VladimirBioACS/VU-meter-IR-control/include/ArduinoJson-v6.19.4.h

// ArduinoJson - https://arduinojson.org
// Copyright © 2014-2022, Benoit BLANCHON
// MIT License

#pragma once

#ifdef __cplusplus

#if __cplusplus >= 201103L
#  define ARDUINOJSON_HAS_LONG_LONG 1
#  define ARDUINOJSON_HAS_RVALUE_REFERENCES 1
#else
#  define ARDUINOJSON_HAS_LONG_LONG 0
#  define ARDUINOJSON_HAS_RVALUE_REFERENCES 0
#endif
#ifndef ARDUINOJSON_HAS_NULLPTR
#  if __cplusplus >= 201103L
#    define ARDUINOJSON_HAS_NULLPTR 1
#  else
#    define ARDUINOJSON_HAS_NULLPTR 0
#  endif
#endif
#if defined(_MSC_VER) && !ARDUINOJSON_HAS_LONG_LONG
#  define ARDUINOJSON_HAS_INT64 1
#else
#  define ARDUINOJSON_HAS_INT64 0
#endif
#ifndef ARDUINOJSON_ENABLE_STD_STREAM
#  ifdef __has_include
#    if __has_include(<istream>) && \
    __has_include(<ostream>) && \
    !defined(min) && \
    !defined(max)
#      define ARDUINOJSON_ENABLE_STD_STREAM 1
#    else
#      define ARDUINOJSON_ENABLE_STD_STREAM 0
#    endif
#  else
#    ifdef ARDUINO
#      define ARDUINOJSON_ENABLE_STD_STREAM 0
#    else
#      define ARDUINOJSON_ENABLE_STD_STREAM 1
#    endif
#  endif
#endif
#ifndef ARDUINOJSON_ENABLE_STD_STRING
#  ifdef __has_include
#    if __has_include(<string>) && !defined(min) && !defined(max)
#      define ARDUINOJSON_ENABLE_STD_STRING 1
#    else
#      define ARDUINOJSON_ENABLE_STD_STRING 0
#    endif
#  else
#    ifdef ARDUINO
#      define ARDUINOJSON_ENABLE_STD_STRING 0
#    else
#      define ARDUINOJSON_ENABLE_STD_STRING 1
#    endif
#  endif
#endif
#ifndef ARDUINOJSON_ENABLE_STRING_VIEW
#  ifdef __has_include
#    if __has_include(<string_view>) && __cplusplus >= 201703L
#      define ARDUINOJSON_ENABLE_STRING_VIEW 1
#    else
#      define ARDUINOJSON_ENABLE_STRING_VIEW 0
#    endif
#  else
#    define ARDUINOJSON_ENABLE_STRING_VIEW 0
#  endif
#endif
#ifndef ARDUINOJSON_USE_DOUBLE
#  define ARDUINOJSON_USE_DOUBLE 1
#endif
#ifndef ARDUINOJSON_USE_LONG_LONG
#  if ARDUINOJSON_HAS_LONG_LONG && defined(__SIZEOF_POINTER__) && \
          __SIZEOF_POINTER__ >= 4 ||                              \
      defined(_MSC_VER)
#    define ARDUINOJSON_USE_LONG_LONG 1
#  endif
#endif
#ifndef ARDUINOJSON_USE_LONG_LONG
#  define ARDUINOJSON_USE_LONG_LONG 0
#endif
#ifndef ARDUINOJSON_DEFAULT_NESTING_LIMIT
#  define ARDUINOJSON_DEFAULT_NESTING_LIMIT 10
#endif
#ifndef ARDUINOJSON_SLOT_OFFSET_SIZE
#  if defined(__SIZEOF_POINTER__) && __SIZEOF_POINTER__ <= 2
#    define ARDUINOJSON_SLOT_OFFSET_SIZE 1
#  elif defined(__SIZEOF_POINTER__) && __SIZEOF_POINTER__ >= 8 || \
      defined(_WIN64) && _WIN64
#    define ARDUINOJSON_SLOT_OFFSET_SIZE 4
#  else
#    define ARDUINOJSON_SLOT_OFFSET_SIZE 2
#  endif
#endif
#ifdef ARDUINO
#  ifndef ARDUINOJSON_ENABLE_ARDUINO_STRING
#    define ARDUINOJSON_ENABLE_ARDUINO_STRING 1
#  endif
#  ifndef ARDUINOJSON_ENABLE_ARDUINO_STREAM
#    define ARDUINOJSON_ENABLE_ARDUINO_STREAM 1
#  endif
#  ifndef ARDUINOJSON_ENABLE_ARDUINO_PRINT
#    define ARDUINOJSON_ENABLE_ARDUINO_PRINT 1
#  endif
#  ifndef ARDUINOJSON_ENABLE_PROGMEM
#    define ARDUINOJSON_ENABLE_PROGMEM 1
#  endif
#else  // ARDUINO
#  ifndef ARDUINOJSON_ENABLE_ARDUINO_STRING
#    define ARDUINOJSON_ENABLE_ARDUINO_STRING 0
#  endif
#  ifndef ARDUINOJSON_ENABLE_ARDUINO_STREAM
#    define ARDUINOJSON_ENABLE_ARDUINO_STREAM 0
#  endif
#  ifndef ARDUINOJSON_ENABLE_ARDUINO_PRINT
#    define ARDUINOJSON_ENABLE_ARDUINO_PRINT 0
#  endif
#  ifndef ARDUINOJSON_ENABLE_PROGMEM
#    define ARDUINOJSON_ENABLE_PROGMEM 0
#  endif
#endif  // ARDUINO
#ifndef ARDUINOJSON_DECODE_UNICODE
#  define ARDUINOJSON_DECODE_UNICODE 1
#endif
#ifndef ARDUINOJSON_ENABLE_COMMENTS
#  define ARDUINOJSON_ENABLE_COMMENTS 0
#endif
#ifndef ARDUINOJSON_ENABLE_NAN
#  define ARDUINOJSON_ENABLE_NAN 0
#endif
#ifndef ARDUINOJSON_ENABLE_INFINITY
#  define ARDUINOJSON_ENABLE_INFINITY 0
#endif
#ifndef ARDUINOJSON_POSITIVE_EXPONENTIATION_THRESHOLD
#  define ARDUINOJSON_POSITIVE_EXPONENTIATION_THRESHOLD 1e7
#endif
#ifndef ARDUINOJSON_NEGATIVE_EXPONENTIATION_THRESHOLD
#  define ARDUINOJSON_NEGATIVE_EXPONENTIATION_THRESHOLD 1e-5
#endif
#ifndef ARDUINOJSON_LITTLE_ENDIAN
#  if defined(_MSC_VER) ||                           \
      (defined(__BYTE_ORDER__) &&                    \
       __BYTE_ORDER__ == __ORDER_LITTLE_ENDIAN__) || \
      defined(__LITTLE_ENDIAN__) || defined(__i386) || defined(__x86_64)
#    define ARDUINOJSON_LITTLE_ENDIAN 1
#  else
#    define ARDUINOJSON_LITTLE_ENDIAN 0
#  endif
#endif
#ifndef ARDUINOJSON_ENABLE_ALIGNMENT
#  if defined(__AVR)
#    define ARDUINOJSON_ENABLE_ALIGNMENT 0
#  else
#    define ARDUINOJSON_ENABLE_ALIGNMENT 1
#  endif
#endif
#ifndef ARDUINOJSON_TAB
#  define ARDUINOJSON_TAB "  "
#endif
#ifndef ARDUINOJSON_ENABLE_STRING_DEDUPLICATION
#  define ARDUINOJSON_ENABLE_STRING_DEDUPLICATION 1
#endif
#ifndef ARDUINOJSON_STRING_BUFFER_SIZE
#  define ARDUINOJSON_STRING_BUFFER_SIZE 32
#endif
#ifndef ARDUINOJSON_DEBUG
#  ifdef __PLATFORMIO_BUILD_DEBUG__
#    define ARDUINOJSON_DEBUG 1
#  else
#    define ARDUINOJSON_DEBUG 0
#  endif
#endif
#if ARDUINOJSON_HAS_NULLPTR && defined(nullptr)
#  error nullptr is defined as a macro. Remove the faulty #define or #undef nullptr
#endif
#if ARDUINOJSON_ENABLE_ARDUINO_STRING || ARDUINOJSON_ENABLE_ARDUINO_STREAM || \
    ARDUINOJSON_ENABLE_ARDUINO_PRINT || ARDUINOJSON_ENABLE_PROGMEM
#include <Arduino.h>
#endif
#if !ARDUINOJSON_DEBUG
#  ifdef __clang__
#    pragma clang system_header
#  elif defined __GNUC__
#    pragma GCC system_header
#  endif
#endif
#define ARDUINOJSON_EXPAND6(a, b, c, d, e, f) a, b, c, d, e, f
#define ARDUINOJSON_EXPAND9(a, b, c, d, e, f, g, h, i) a, b, c, d, e, f, g, h, i
#define ARDUINOJSON_EXPAND18(a, b, c, d, e, f, g, h, i, j, k, l, m, n, o, p, \
                             q, r)                                           \
  a, b, c, d, e, f, g, h, i, j, k, l, m, n, o, p, q, r
#define ARDUINOJSON_CONCAT_(A, B) A##B
#define ARDUINOJSON_CONCAT2(A, B) ARDUINOJSON_CONCAT_(A, B)
#define ARDUINOJSON_CONCAT4(A, B, C, D) \
  ARDUINOJSON_CONCAT2(ARDUINOJSON_CONCAT2(A, B), ARDUINOJSON_CONCAT2(C, D))
#define ARDUINOJSON_HEX_DIGIT_0000() 0
#define ARDUINOJSON_HEX_DIGIT_0001() 1
#define ARDUINOJSON_HEX_DIGIT_0010() 2
#define ARDUINOJSON_HEX_DIGIT_0011() 3
#define ARDUINOJSON_HEX_DIGIT_0100() 4
#define ARDUINOJSON_HEX_DIGIT_0101() 5
#define ARDUINOJSON_HEX_DIGIT_0110() 6
#define ARDUINOJSON_HEX_DIGIT_0111() 7
#define ARDUINOJSON_HEX_DIGIT_1000() 8
#define ARDUINOJSON_HEX_DIGIT_1001() 9
#define ARDUINOJSON_HEX_DIGIT_1010() A
#define ARDUINOJSON_HEX_DIGIT_1011() B
#define ARDUINOJSON_HEX_DIGIT_1100() C
#define ARDUINOJSON_HEX_DIGIT_1101() D
#define ARDUINOJSON_HEX_DIGIT_1110() E
#define ARDUINOJSON_HEX_DIGIT_1111() F
#define ARDUINOJSON_HEX_DIGIT_(A, B, C, D) ARDUINOJSON_HEX_DIGIT_##A##B##C##D()
#define ARDUINOJSON_HEX_DIGIT(A, B, C, D) ARDUINOJSON_HEX_DIGIT_(A, B, C, D)
#define ARDUINOJSON_VERSION "6.19.4"
#define ARDUINOJSON_VERSION_MAJOR 6
#define ARDUINOJSON_VERSION_MINOR 19
#define ARDUINOJSON_VERSION_REVISION 4
#ifndef ARDUINOJSON_NAMESPACE
#  define ARDUINOJSON_NAMESPACE                                               \
    ARDUINOJSON_CONCAT4(                                                      \
        ARDUINOJSON_CONCAT4(ArduinoJson, ARDUINOJSON_VERSION_MAJOR,           \
                            ARDUINOJSON_VERSION_MINOR,                        \
                            ARDUINOJSON_VERSION_REVISION),                    \
        _,                                                                    \
        ARDUINOJSON_HEX_DIGIT(                                                \
            ARDUINOJSON_ENABLE_PROGMEM, ARDUINOJSON_USE_LONG_LONG,            \
            ARDUINOJSON_USE_DOUBLE, ARDUINOJSON_ENABLE_STRING_DEDUPLICATION), \
        ARDUINOJSON_HEX_DIGIT(                                                \
            ARDUINOJSON_ENABLE_NAN, ARDUINOJSON_ENABLE_INFINITY,              \
            ARDUINOJSON_ENABLE_COMMENTS, ARDUINOJSON_DECODE_UNICODE))
#endif
#if ARDUINOJSON_DEBUG
#include <assert.h>
#  define ARDUINOJSON_ASSERT(X) assert(X)
#else
#  define ARDUINOJSON_ASSERT(X) ((void)0)
#endif
#include <stddef.h>
namespace ARDUINOJSON_NAMESPACE {
class MemoryPool;
class VariantData;
class VariantSlot;
class CollectionData {
  VariantSlot *_head;
  VariantSlot *_tail;
 public:
  VariantData *addElement(MemoryPool *pool);
  VariantData *getElement(size_t index) const;
  VariantData *getOrAddElement(size_t index, MemoryPool *pool);
  void removeElement(size_t index);
  bool equalsArray(const CollectionData &other) const;
  template <typename TAdaptedString, typename TStoragePolicy>
  VariantData *addMember(TAdaptedString key, MemoryPool *pool, TStoragePolicy);
  template <typename TAdaptedString>
  VariantData *getMember(TAdaptedString key) const;
  template <typename TAdaptedString, typename TStoragePolicy>
  VariantData *getOrAddMember(TAdaptedString key, MemoryPool *pool,
                              TStoragePolicy);
  template <typename TAdaptedString>
  void removeMember(TAdaptedString key) {
    removeSlot(getSlot(key));
  }
  template <typename TAdaptedString>
  bool containsKey(const TAdaptedString &key) const;
  bool equalsObject(const CollectionData &other) const;
  void clear();
  size_t memoryUsage() const;
  size_t nesting() const;
  size_t size() const;
  VariantSlot *addSlot(MemoryPool *);
  void removeSlot(VariantSlot *slot);
  bool copyFrom(const CollectionData &src, MemoryPool *pool);
  VariantSlot *head() const {
    return _head;
  }
  void movePointers(ptrdiff_t stringDistance, ptrdiff_t variantDistance);
 private:
  VariantSlot *getSlot(size_t index) const;
  template <typename TAdaptedString>
  VariantSlot *getSlot(TAdaptedString key) const;
  VariantSlot *getPreviousSlot(VariantSlot *) const;
};
inline VariantData *arrayAdd(CollectionData *arr, MemoryPool *pool) {
  return arr ? arr->addElement(pool) : 0;
}
template <typename TVisitor>
inline typename TVisitor::result_type arrayAccept(const CollectionData *arr,
                                                  TVisitor &visitor) {
  if (arr)
    return visitor.visitArray(*arr);
  else
    return visitor.visitNull();
}
inline bool arrayEquals(const CollectionData *lhs, const CollectionData *rhs) {
  if (lhs == rhs)
    return true;
  if (!lhs || !rhs)
    return false;
  return lhs->equalsArray(*rhs);
}
#if ARDUINOJSON_ENABLE_ALIGNMENT
inline bool isAligned(size_t value) {
  const size_t mask = sizeof(void *) - 1;
  size_t addr = value;
  return (addr & mask) == 0;
}
inline size_t addPadding(size_t bytes) {
  const size_t mask = sizeof(void *) - 1;
  return (bytes + mask) & ~mask;
}
template <size_t bytes>
struct AddPadding {
  static const size_t mask = sizeof(void *) - 1;
  static const size_t value = (bytes + mask) & ~mask;
};
#else
inline bool isAligned(size_t) {
  return true;
}
inline size_t addPadding(size_t bytes) {
  return bytes;
}
template <size_t bytes>
struct AddPadding {
  static const size_t value = bytes;
};
#endif
template <typename T>
inline bool isAligned(T *ptr) {
  return isAligned(reinterpret_cast<size_t>(ptr));
}
template <typename T>
inline T *addPadding(T *p) {
  size_t address = addPadding(reinterpret_cast<size_t>(p));
  return reinterpret_cast<T *>(address);
}
template <size_t X, size_t Y, bool MaxIsX = (X > Y)>
struct Max {};
template <size_t X, size_t Y>
struct Max<X, Y, true> {
  static const size_t value = X;
};
template <size_t X, size_t Y>
struct Max<X, Y, false> {
  static const size_t value = Y;
};
template <bool Condition, class TrueType, class FalseType>
struct conditional {
  typedef TrueType type;
};
template <class TrueType, class FalseType>
struct conditional<false, TrueType, FalseType> {
  typedef FalseType type;
};
template <bool Condition, typename T = void>
struct enable_if {};
template <typename T>
struct enable_if<true, T> {
  typedef T type;
};
template <typename T, T v>
struct integral_constant {
  static const T value = v;
};
typedef integral_constant<bool, true> true_type;
typedef integral_constant<bool, false> false_type;
template <typename T>
struct is_array : false_type {};
template <typename T>
struct is_array<T[]> : true_type {};
template <typename T, size_t N>
struct is_array<T[N]> : true_type {};
template <typename TBase, typename TDerived>
class is_base_of {
 protected:  // <- to avoid GCC's "all member functions in class are private"
  typedef char Yes[1];
  typedef char No[2];
  static Yes &probe(const TBase *);
  static No &probe(...);
 public:
  static const bool value =
      sizeof(probe(reinterpret_cast<TDerived *>(0))) == sizeof(Yes);
};
template <typename T>
T declval();
template <typename T>
struct is_class {
 protected:  // <- to avoid GCC's "all member functions in class are private"
  typedef char Yes[1];
  typedef char No[2];
  template <typename U>
  static Yes &probe(void (U::*)(void));
  template <typename>
  static No &probe(...);
 public:
  static const bool value = sizeof(probe<T>(0)) == sizeof(Yes);
};
template <typename T>
struct is_const : false_type {};
template <typename T>
struct is_const<const T> : true_type {};
}  // namespace ARDUINOJSON_NAMESPACE
#ifdef _MSC_VER
#  pragma warning(push)
#  pragma warning(disable : 4244)
#endif
#ifdef __ICCARM__
#pragma diag_suppress=Pa093
#endif
namespace ARDUINOJSON_NAMESPACE {
template <typename From, typename To>
struct is_convertible {
 protected:  // <- to avoid GCC's "all member functions in class are private"
  typedef char Yes[1];
  typedef char No[2];
  static Yes &probe(To);
  static No &probe(...);
 public:
  static const bool value = sizeof(probe(declval<From>())) == sizeof(Yes);
};
}  // namespace ARDUINOJSON_NAMESPACE
#ifdef _MSC_VER
#  pragma warning(pop)
#endif
#ifdef __ICCARM__
#pragma diag_default=Pa093
#endif
namespace ARDUINOJSON_NAMESPACE {
template <typename T, typename U>
struct is_same : false_type {};
template <typename T>
struct is_same<T, T> : true_type {};
template <typename T>
struct remove_cv {
  typedef T type;
};
template <typename T>
struct remove_cv<const T> {
  typedef T type;
};
template <typename T>
struct remove_cv<volatile T> {
  typedef T type;
};
template <typename T>
struct remove_cv<const volatile T> {
  typedef T type;
};
template <class T>
struct is_floating_point
    : integral_constant<
          bool,  //
          is_same<float, typename remove_cv<T>::type>::value ||
              is_same<double, typename remove_cv<T>::type>::value> {};
template <typename T>
struct is_integral : integral_constant<bool,
    is_same<typename remove_cv<T>::type, signed char>::value ||
    is_same<typename remove_cv<T>::type, unsigned char>::value ||
    is_same<typename remove_cv<T>::type, signed short>::value ||
    is_same<typename remove_cv<T>::type, unsigned short>::value ||
    is_same<typename remove_cv<T>::type, signed int>::value ||
    is_same<typename remove_cv<T>::type, unsigned int>::value ||
    is_same<typename remove_cv<T>::type, signed long>::value ||
    is_same<typename remove_cv<T>::type, unsigned long>::value ||
#if ARDUINOJSON_HAS_LONG_LONG
    is_same<typename remove_cv<T>::type, signed long long>::value ||
    is_same<typename remove_cv<T>::type, unsigned long long>::value ||
#endif
#if ARDUINOJSON_HAS_INT64
    is_same<typename remove_cv<T>::type, signed __int64>::value ||
    is_same<typename remove_cv<T>::type, unsigned __int64>::value ||
#endif
    is_same<typename remove_cv<T>::type, char>::value ||
    is_same<typename remove_cv<T>::type, bool>::value> {};
template <typename T>
struct is_enum {
  static const bool value = is_convertible<T, int>::value &&
                            !is_class<T>::value && !is_integral<T>::value &&
                            !is_floating_point<T>::value;
};
template <typename T>
struct is_pointer : false_type {};
template <typename T>
struct is_pointer<T*> : true_type {};
template <typename T>
struct is_signed : integral_constant<bool, 
    is_same<typename remove_cv<T>::type, char>::value ||
    is_same<typename remove_cv<T>::type, signed char>::value ||
    is_same<typename remove_cv<T>::type, signed short>::value ||
    is_same<typename remove_cv<T>::type, signed int>::value ||
    is_same<typename remove_cv<T>::type, signed long>::value ||
#if ARDUINOJSON_HAS_LONG_LONG
    is_same<typename remove_cv<T>::type, signed long long>::value ||
#endif
#if ARDUINOJSON_HAS_INT64
    is_same<typename remove_cv<T>::type, signed __int64>::value ||
#endif
    is_same<typename remove_cv<T>::type, float>::value ||
    is_same<typename remove_cv<T>::type, double>::value> {};
template <typename T>
struct is_unsigned : integral_constant<bool,
    is_same<typename remove_cv<T>::type, unsigned char>::value ||
    is_same<typename remove_cv<T>::type, unsigned short>::value ||
    is_same<typename remove_cv<T>::type, unsigned int>::value ||
    is_same<typename remove_cv<T>::type, unsigned long>::value ||
#if ARDUINOJSON_HAS_INT64
    is_same<typename remove_cv<T>::type, unsigned __int64>::value ||
#endif
#if ARDUINOJSON_HAS_LONG_LONG
    is_same<typename remove_cv<T>::type, unsigned long long>::value ||
#endif
    is_same<typename remove_cv<T>::type, bool>::value> {};
template <typename T>
struct type_identity {
  typedef T type;
};
template <typename T>
struct make_unsigned;
template <>
struct make_unsigned<char> : type_identity<unsigned char> {};
template <>
struct make_unsigned<signed char> : type_identity<unsigned char> {};
template <>
struct make_unsigned<unsigned char> : type_identity<unsigned char> {};
template <>
struct make_unsigned<signed short> : type_identity<unsigned short> {};
template <>
struct make_unsigned<unsigned short> : type_identity<unsigned short> {};
template <>
struct make_unsigned<signed int> : type_identity<unsigned int> {};
template <>
struct make_unsigned<unsigned int> : type_identity<unsigned int> {};
template <>
struct make_unsigned<signed long> : type_identity<unsigned long> {};
template <>
struct make_unsigned<unsigned long> : type_identity<unsigned long> {};
#if ARDUINOJSON_HAS_LONG_LONG
template <>
struct make_unsigned<signed long long> : type_identity<unsigned long long> {};
template <>
struct make_unsigned<unsigned long long> : type_identity<unsigned long long> {};
#endif
#if ARDUINOJSON_HAS_INT64
template <>
struct make_unsigned<signed __int64> : type_identity<unsigned __int64> {};
template <>
struct make_unsigned<unsigned __int64> : type_identity<unsigned __int64> {};
#endif
template <class = void>
struct make_void {
  typedef void type;
};
template <typename T>
struct remove_const {
  typedef T type;
};
template <typename T>
struct remove_const<const T> {
  typedef T type;
};
template <typename T>
struct remove_reference {
  typedef T type;
};
template <typename T>
struct remove_reference<T&> {
  typedef T type;
};
}  // namespace ARDUINOJSON_NAMESPACE
#include <string.h>
namespace ARDUINOJSON_NAMESPACE {
template <typename T, typename Enable = void>
struct IsString : false_type {};
template <typename TChar>
struct IsString<const TChar*> : IsString<TChar*> {};
class ZeroTerminatedRamString {
 public:
  static const size_t typeSortKey = 3;
  ZeroTerminatedRamString(const char* str) : _str(str) {}
  bool isNull() const {
    return !_str;
  }
  size_t size() const {
    return _str ? ::strlen(_str) : 0;
  }
  char operator[](size_t i) const {
    ARDUINOJSON_ASSERT(_str != 0);
    ARDUINOJSON_ASSERT(i <= size());
    return _str[i];
  }
  const char* data() const {
    return _str;
  }
  friend int stringCompare(ZeroTerminatedRamString a,
                           ZeroTerminatedRamString b) {
    ARDUINOJSON_ASSERT(!a.isNull());
    ARDUINOJSON_ASSERT(!b.isNull());
    return ::strcmp(a._str, b._str);
  }
  friend bool stringEquals(ZeroTerminatedRamString a,
                           ZeroTerminatedRamString b) {
    return stringCompare(a, b) == 0;
  }
 protected:
  const char* _str;
};
template <>
struct IsString<char*> : true_type {};
inline ZeroTerminatedRamString adaptString(const char* s) {
  return ZeroTerminatedRamString(s);
}
template <>
struct IsString<unsigned char*> : true_type {};
inline ZeroTerminatedRamString adaptString(const unsigned char* s) {
  return adaptString(reinterpret_cast<const char*>(s));
}
template <>
struct IsString<signed char*> : true_type {};
inline ZeroTerminatedRamString adaptString(const signed char* s) {
  return adaptString(reinterpret_cast<const char*>(s));
}
class SizedRamString {
 public:
  static const size_t typeSortKey = 2;
  SizedRamString(const char* str, size_t sz) : _str(str), _size(sz) {}
  bool isNull() const {
    return !_str;
  }
  size_t size() const {
    return _size;
  }
  char operator[](size_t i) const {
    ARDUINOJSON_ASSERT(_str != 0);
    ARDUINOJSON_ASSERT(i <= size());
    return _str[i];
  }
  const char* data() const {
    return _str;
  }
 protected:
  const char* _str;
  size_t _size;
};
inline SizedRamString adaptString(const char* s, size_t n) {
  return SizedRamString(s, n);
}
template <size_t N>
struct IsString<char[N]> : true_type {};
template <size_t N>
struct IsString<const char[N]> : true_type {};
template <size_t N>
inline SizedRamString adaptString(char s[N]) {
  return SizedRamString(s, strlen(s));
}
template <typename T>
class SafeBoolIdom {
 protected:
  typedef void (T::*bool_type)() const;
  void safeBoolHelper() const {}
  static bool_type safe_true() {
    return &SafeBoolIdom::safeBoolHelper;
  }
  static bool_type safe_false() {
    return 0;
  }
};
}  // namespace ARDUINOJSON_NAMESPACE
#if ARDUINOJSON_ENABLE_STD_STREAM
#include <ostream>
#endif
namespace ARDUINOJSON_NAMESPACE {
class String : public SafeBoolIdom<String> {
 public:
  enum Ownership { Copied, Linked };
  String() : _data(0), _size(0), _ownership(Linked) {}
  String(const char* data, Ownership ownership = Linked)
      : _data(data), _size(data ? ::strlen(data) : 0), _ownership(ownership) {}
  String(const char* data, size_t sz, Ownership ownership = Linked)
      : _data(data), _size(sz), _ownership(ownership) {}
  const char* c_str() const {
    return _data;
  }
  bool isNull() const {
    return !_data;
  }
  bool isLinked() const {
    return _ownership == Linked;
  }
  size_t size() const {
    return _size;
  }
  operator bool_type() const {
    return _data ? safe_true() : safe_false();
  }
  friend bool operator==(String lhs, String rhs) {
    if (lhs._size != rhs._size)
      return false;
    if (lhs._data == rhs._data)
      return true;
    if (!lhs._data)
      return false;
    if (!rhs._data)
      return false;
    return memcmp(lhs._data, rhs._data, lhs._size) == 0;
  }
  friend bool operator!=(String lhs, String rhs) {
    return !(lhs == rhs);
  }
#if ARDUINOJSON_ENABLE_STD_STREAM
  friend std::ostream& operator<<(std::ostream& lhs, const String& rhs) {
    lhs.write(rhs.c_str(), static_cast<std::streamsize>(rhs.size()));
    return lhs;
  }
#endif
 private:
  const char* _data;
  size_t _size;
  Ownership _ownership;
};
inline SizedRamString adaptString(const String& s) {
  return SizedRamString(s.c_str(), s.size());
}
template <>
struct IsString<String> : true_type {};
}  // namespace ARDUINOJSON_NAMESPACE
#if ARDUINOJSON_ENABLE_STD_STRING
#include <string>
namespace ARDUINOJSON_NAMESPACE {
template <typename TCharTraits, typename TAllocator>
inline SizedRamString adaptString(
    const std::basic_string<char, TCharTraits, TAllocator>& s) {
  return SizedRamString(s.c_str(), s.size());
}
template <typename TCharTraits, typename TAllocator>
struct IsString<std::basic_string<char, TCharTraits, TAllocator> > : true_type {
};
}  // namespace ARDUINOJSON_NAMESPACE
#endif
#if ARDUINOJSON_ENABLE_STRING_VIEW
#include <string_view>
namespace ARDUINOJSON_NAMESPACE {
inline SizedRamString adaptString(const std::string_view& s) {
  return SizedRamString(s.data(), s.size());
}
template <>
struct IsString<std::string_view> : true_type {};
}  // namespace ARDUINOJSON_NAMESPACE
#endif
#if ARDUINOJSON_ENABLE_ARDUINO_STRING
namespace ARDUINOJSON_NAMESPACE {
inline SizedRamString adaptString(const ::String& s) {
  return SizedRamString(s.c_str(), s.length());
}
template <>
struct IsString< ::String> : true_type {};
template <>
struct IsString< ::StringSumHelper> : true_type {};
}  // namespace ARDUINOJSON_NAMESPACE
#endif
#if ARDUINOJSON_ENABLE_PROGMEM
namespace ARDUINOJSON_NAMESPACE {
struct pgm_p {
  pgm_p(const void* p) : address(reinterpret_cast<const char*>(p)) {}
  const char* address;
};
}  // namespace ARDUINOJSON_NAMESPACE
#ifndef strlen_P
inline size_t strlen_P(ARDUINOJSON_NAMESPACE::pgm_p s) {
  const char* p = s.address;
  ARDUINOJSON_ASSERT(p != NULL);
  while (pgm_read_byte(p)) p++;
  return size_t(p - s.address);
}
#endif
#ifndef strncmp_P
inline int strncmp_P(const char* a, ARDUINOJSON_NAMESPACE::pgm_p b, size_t n) {
  const char* s1 = a;
  const char* s2 = b.address;
  ARDUINOJSON_ASSERT(s1 != NULL);
  ARDUINOJSON_ASSERT(s2 != NULL);
  while (n-- > 0) {
    char c1 = *s1++;
    char c2 = static_cast<char>(pgm_read_byte(s2++));
    if (c1 < c2)
      return -1;
    if (c1 > c2)
      return 1;
    if (c1 == 0 /* and c2 as well */)
      return 0;
  }
  return 0;
}
#endif
#ifndef strcmp_P
inline int strcmp_P(const char* a, ARDUINOJSON_NAMESPACE::pgm_p b) {
  const char* s1 = a;
  const char* s2 = b.address;
  ARDUINOJSON_ASSERT(s1 != NULL);
  ARDUINOJSON_ASSERT(s2 != NULL);
  for (;;) {
    char c1 = *s1++;
    char c2 = static_cast<char>(pgm_read_byte(s2++));
    if (c1 < c2)
      return -1;
    if (c1 > c2)
      return 1;
    if (c1 == 0 /* and c2 as well */)
      return 0;
  }
}
#endif
#ifndef memcmp_P
inline int memcmp_P(const void* a, ARDUINOJSON_NAMESPACE::pgm_p b, size_t n) {
  const uint8_t* p1 = reinterpret_cast<const uint8_t*>(a);
  const char* p2 = b.address;
  ARDUINOJSON_ASSERT(p1 != NULL);
  ARDUINOJSON_ASSERT(p2 != NULL);
  while (n-- > 0) {
    uint8_t v1 = *p1++;
    uint8_t v2 = pgm_read_byte(p2++);
    if (v1 != v2)
      return v1 - v2;
  }
  return 0;
}
#endif
#ifndef memcpy_P
inline void* memcpy_P(void* dst, ARDUINOJSON_NAMESPACE::pgm_p src, size_t n) {
  uint8_t* d = reinterpret_cast<uint8_t*>(dst);
  const char* s = src.address;
  ARDUINOJSON_ASSERT(d != NULL);
  ARDUINOJSON_ASSERT(s != NULL);
  while (n-- > 0) {
    *d++ = pgm_read_byte(s++);
  }
  return dst;
}
#endif
#ifndef pgm_read_dword
inline uint32_t pgm_read_dword(ARDUINOJSON_NAMESPACE::pgm_p p) {
  uint32_t result;
  memcpy_P(&result, p.address, 4);
  return result;
}
#endif
#ifndef pgm_read_ptr
inline void* pgm_read_ptr(ARDUINOJSON_NAMESPACE::pgm_p p) {
  void* result;
  memcpy_P(&result, p.address, sizeof(result));
  return result;
}
#endif
namespace ARDUINOJSON_NAMESPACE {
class FlashString {
 public:
  static const size_t typeSortKey = 1;
  FlashString(const __FlashStringHelper* str, size_t sz)
      : _str(reinterpret_cast<const char*>(str)), _size(sz) {}
  bool isNull() const {
    return !_str;
  }
  char operator[](size_t i) const {
    ARDUINOJSON_ASSERT(_str != 0);
    ARDUINOJSON_ASSERT(i <= _size);
    return static_cast<char>(pgm_read_byte(_str + i));
  }
  size_t size() const {
    return _size;
  }
  friend bool stringEquals(FlashString a, SizedRamString b) {
    ARDUINOJSON_ASSERT(a.typeSortKey < b.typeSortKey);
    ARDUINOJSON_ASSERT(!a.isNull());
    ARDUINOJSON_ASSERT(!b.isNull());
    if (a.size() != b.size())
      return false;
    return ::memcmp_P(b.data(), a._str, a._size) == 0;
  }
  friend int stringCompare(FlashString a, SizedRamString b) {
    ARDUINOJSON_ASSERT(a.typeSortKey < b.typeSortKey);
    ARDUINOJSON_ASSERT(!a.isNull());
    ARDUINOJSON_ASSERT(!b.isNull());
    size_t minsize = a.size() < b.size() ? a.size() : b.size();
    int res = ::memcmp_P(b.data(), a._str, minsize);
    if (res)
      return -res;
    if (a.size() < b.size())
      return -1;
    if (a.size() > b.size())
      return 1;
    return 0;
  }
  friend void stringGetChars(FlashString s, char* p, size_t n) {
    ARDUINOJSON_ASSERT(s.size() <= n);
    ::memcpy_P(p, s._str, n);
  }
 private:
  const char* _str;
  size_t _size;
};
inline FlashString adaptString(const __FlashStringHelper* s) {
  return FlashString(s, s ? strlen_P(reinterpret_cast<const char*>(s)) : 0);
}
inline FlashString adaptString(const __FlashStringHelper* s, size_t n) {
  return FlashString(s, n);
}
template <>
struct IsString<const __FlashStringHelper*> : true_type {};
}  // namespace ARDUINOJSON_NAMESPACE
#endif
namespace ARDUINOJSON_NAMESPACE {
template <typename TAdaptedString1, typename TAdaptedString2>
typename enable_if<TAdaptedString1::typeSortKey <= TAdaptedString2::typeSortKey,
                   int>::type
stringCompare(TAdaptedString1 s1, TAdaptedString2 s2) {
  ARDUINOJSON_ASSERT(!s1.isNull());
  ARDUINOJSON_ASSERT(!s2.isNull());
  size_t size1 = s1.size();
  size_t size2 = s2.size();
  size_t n = size1 < size2 ? size1 : size2;
  for (size_t i = 0; i < n; i++) {
    if (s1[i] != s2[i])
      return s1[i] - s2[i];
  }
  if (size1 < size2)
    return -1;
  if (size1 > size2)
    return 1;
  return 0;
}
template <typename TAdaptedString1, typename TAdaptedString2>
typename enable_if<
    (TAdaptedString1::typeSortKey > TAdaptedString2::typeSortKey), int>::type
stringCompare(TAdaptedString1 s1, TAdaptedString2 s2) {
  return -stringCompare(s2, s1);
}
template <typename TAdaptedString1, typename TAdaptedString2>
typename enable_if<TAdaptedString1::typeSortKey <= TAdaptedString2::typeSortKey,
                   bool>::type
stringEquals(TAdaptedString1 s1, TAdaptedString2 s2) {
  ARDUINOJSON_ASSERT(!s1.isNull());
  ARDUINOJSON_ASSERT(!s2.isNull());
  size_t size1 = s1.size();
  size_t size2 = s2.size();
  if (size1 != size2)
    return false;
  for (size_t i = 0; i < size1; i++) {
    if (s1[i] != s2[i])
      return false;
  }
  return true;
}
template <typename TAdaptedString1, typename TAdaptedString2>
typename enable_if<
    (TAdaptedString1::typeSortKey > TAdaptedString2::typeSortKey), bool>::type
stringEquals(TAdaptedString1 s1, TAdaptedString2 s2) {
  return stringEquals(s2, s1);
}
template <typename TAdaptedString>
static void stringGetChars(TAdaptedString s, char* p, size_t n) {
  ARDUINOJSON_ASSERT(s.size() <= n);
  for (size_t i = 0; i < n; i++) {
    p[i] = s[i];
  }
}
}  // namespace ARDUINOJSON_NAMESPACE
#include <stdint.h>
namespace ARDUINOJSON_NAMESPACE {
template <int Bits>
struct int_t;
template <>
struct int_t<8> {
  typedef int8_t type;
};
template <>
struct int_t<16> {
  typedef int16_t type;
};
template <>
struct int_t<32> {
  typedef int32_t type;
};
}  // namespace ARDUINOJSON_NAMESPACE
#ifdef _MSC_VER
#  pragma warning(push)
#  pragma warning(disable : 4310)
#endif
namespace ARDUINOJSON_NAMESPACE {
template <typename T, typename Enable = void>
struct numeric_limits;
template <typename T>
struct numeric_limits<T, typename enable_if<is_unsigned<T>::value>::type> {
  static T lowest() {
    return 0;
  }
  static T highest() {
    return T(-1);
  }
};
template <typename T>
struct numeric_limits<
    T, typename enable_if<is_integral<T>::value && is_signed<T>::value>::type> {
  static T lowest() {
    return T(T(1) << (sizeof(T) * 8 - 1));
  }
  static T highest() {
    return T(~lowest());
  }
};
}  // namespace ARDUINOJSON_NAMESPACE
#ifdef _MSC_VER
#  pragma warning(pop)
#endif
namespace ARDUINOJSON_NAMESPACE {
#if ARDUINOJSON_USE_DOUBLE
typedef double Float;
#else
typedef float Float;
#endif
#if ARDUINOJSON_USE_LONG_LONG
typedef int64_t Integer;
typedef uint64_t UInt;
#else
typedef long Integer;
typedef unsigned long UInt;
#endif
}  // namespace ARDUINOJSON_NAMESPACE
#if ARDUINOJSON_HAS_LONG_LONG && !ARDUINOJSON_USE_LONG_LONG
#  define ARDUINOJSON_ASSERT_INTEGER_TYPE_IS_SUPPORTED(T)                  \
    static_assert(sizeof(T) <= sizeof(ARDUINOJSON_NAMESPACE::Integer),     \
                  "To use 64-bit integers with ArduinoJson, you must set " \
                  "ARDUINOJSON_USE_LONG_LONG to 1. See "                   \
                  "https://arduinojson.org/v6/api/config/use_long_long/");
#else
#  define ARDUINOJSON_ASSERT_INTEGER_TYPE_IS_SUPPORTED(T)
#endif
namespace ARDUINOJSON_NAMESPACE {
enum {
  VALUE_MASK = 0x7F,
  OWNED_VALUE_BIT = 0x01,
  VALUE_IS_NULL = 0,
  VALUE_IS_LINKED_RAW = 0x02,
  VALUE_IS_OWNED_RAW = 0x03,
  VALUE_IS_LINKED_STRING = 0x04,
  VALUE_IS_OWNED_STRING = 0x05,
  VALUE_IS_BOOLEAN = 0x06,
  NUMBER_BIT = 0x08,
  VALUE_IS_UNSIGNED_INTEGER = 0x08,
  VALUE_IS_SIGNED_INTEGER = 0x0A,
  VALUE_IS_FLOAT = 0x0C,
  COLLECTION_MASK = 0x60,
  VALUE_IS_OBJECT = 0x20,
  VALUE_IS_ARRAY = 0x40,
  OWNED_KEY_BIT = 0x80
};
struct RawData {
  const char *data;
  size_t size;
};
union VariantContent {
  Float asFloat;
  bool asBoolean;
  UInt asUnsignedInteger;
  Integer asSignedInteger;
  CollectionData asCollection;
  struct {
    const char *data;
    size_t size;
  } asString;
};
typedef int_t<ARDUINOJSON_SLOT_OFFSET_SIZE * 8>::type VariantSlotDiff;
class VariantSlot {
  VariantContent _content;
  uint8_t _flags;
  VariantSlotDiff _next;
  const char* _key;
 public:
  VariantData* data() {
    return reinterpret_cast<VariantData*>(&_content);
  }
  const VariantData* data() const {
    return reinterpret_cast<const VariantData*>(&_content);
  }
  VariantSlot* next() {
    return _next ? this + _next : 0;
  }
  const VariantSlot* next() const {
    return const_cast<VariantSlot*>(this)->next();
  }
  VariantSlot* next(size_t distance) {
    VariantSlot* slot = this;
    while (distance--) {
      if (!slot->_next)
        return 0;
      slot += slot->_next;
    }
    return slot;
  }
  const VariantSlot* next(size_t distance) const {
    return const_cast<VariantSlot*>(this)->next(distance);
  }
  void setNext(VariantSlot* slot) {
    ARDUINOJSON_ASSERT(!slot || slot - this >=
                                    numeric_limits<VariantSlotDiff>::lowest());
    ARDUINOJSON_ASSERT(!slot || slot - this <=
                                    numeric_limits<VariantSlotDiff>::highest());
    _next = VariantSlotDiff(slot ? slot - this : 0);
  }
  void setNextNotNull(VariantSlot* slot) {
    ARDUINOJSON_ASSERT(slot != 0);
    ARDUINOJSON_ASSERT(slot - this >=
                       numeric_limits<VariantSlotDiff>::lowest());
    ARDUINOJSON_ASSERT(slot - this <=
                       numeric_limits<VariantSlotDiff>::highest());
    _next = VariantSlotDiff(slot - this);
  }
  void setKey(String k) {
    ARDUINOJSON_ASSERT(k);
    if (k.isLinked())
      _flags &= VALUE_MASK;
    else
      _flags |= OWNED_KEY_BIT;
    _key = k.c_str();
  }
  const char* key() const {
    return _key;
  }
  bool ownsKey() const {
    return (_flags & OWNED_KEY_BIT) != 0;
  }
  void clear() {
    _next = 0;
    _flags = 0;
    _key = 0;
  }
  void movePointers(ptrdiff_t stringDistance, ptrdiff_t variantDistance) {
    if (_flags & OWNED_KEY_BIT)
      _key += stringDistance;
    if (_flags & OWNED_VALUE_BIT)
      _content.asString.data += stringDistance;
    if (_flags & COLLECTION_MASK)
      _content.asCollection.movePointers(stringDistance, variantDistance);
  }
};
}  // namespace ARDUINOJSON_NAMESPACE
#define JSON_STRING_SIZE(SIZE) (SIZE + 1)
namespace ARDUINOJSON_NAMESPACE {
class MemoryPool {
 public:
  MemoryPool(char* buf, size_t capa)
      : _begin(buf),
        _left(buf),
        _right(buf ? buf + capa : 0),
        _end(buf ? buf + capa : 0),
        _overflowed(false) {
    ARDUINOJSON_ASSERT(isAligned(_begin));
    ARDUINOJSON_ASSERT(isAligned(_right));
    ARDUINOJSON_ASSERT(isAligned(_end));
  }
  void* buffer() {
    return _begin;  // NOLINT(clang-analyzer-unix.Malloc)
  }
  size_t capacity() const {
    return size_t(_end - _begin);
  }
  size_t size() const {
    return size_t(_left - _begin + _end - _right);
  }
  bool overflowed() const {
    return _overflowed;
  }
  VariantSlot* allocVariant() {
    return allocRight<VariantSlot>();
  }
  template <typename TAdaptedString>
  const char* saveString(TAdaptedString str) {
    if (str.isNull())
      return 0;
#if ARDUINOJSON_ENABLE_STRING_DEDUPLICATION
    const char* existingCopy = findString(str);
    if (existingCopy)
      return existingCopy;
#endif
    size_t n = str.size();
    char* newCopy = allocString(n + 1);
    if (newCopy) {
      stringGetChars(str, newCopy, n);
      newCopy[n] = 0;  // force null-terminator
    }
    return newCopy;
  }
  void getFreeZone(char** zoneStart, size_t* zoneSize) const {
    *zoneStart = _left;
    *zoneSize = size_t(_right - _left);
  }
  const char* saveStringFromFreeZone(size_t len) {
#if ARDUINOJSON_ENABLE_STRING_DEDUPLICATION
    const char* dup = findString(adaptString(_left, len));
    if (dup)
      return dup;
#endif
    const char* str = _left;
    _left += len;
    *_left++ = 0;
    checkInvariants();
    return str;
  }
  void markAsOverflowed() {
    _overflowed = true;
  }
  void clear() {
    _left = _begin;
    _right = _end;
    _overflowed = false;
  }
  bool canAlloc(size_t bytes) const {
    return _left + bytes <= _right;
  }
  bool owns(void* p) const {
    return _begin <= p && p < _end;
  }
  // void* operator new(size_t, void* p) {
  //   return p;
  // }
  ptrdiff_t squash() {
    char* new_right = addPadding(_left);
    if (new_right >= _right)
      return 0;
    size_t right_size = static_cast<size_t>(_end - _right);
    memmove(new_right, _right, right_size);
    ptrdiff_t bytes_reclaimed = _right - new_right;
    _right = new_right;
    _end = new_right + right_size;
    return bytes_reclaimed;
  }
  void movePointers(ptrdiff_t offset) {
    _begin += offset;
    _left += offset;
    _right += offset;
    _end += offset;
  }
 private:
  void checkInvariants() {
    ARDUINOJSON_ASSERT(_begin <= _left);
    ARDUINOJSON_ASSERT(_left <= _right);
    ARDUINOJSON_ASSERT(_right <= _end);
    ARDUINOJSON_ASSERT(isAligned(_right));
  }
#if ARDUINOJSON_ENABLE_STRING_DEDUPLICATION
  template <typename TAdaptedString>
  const char* findString(const TAdaptedString& str) const {
    size_t n = str.size();
    for (char* next = _begin; next + n < _left; ++next) {
      if (next[n] == '\0' && stringEquals(str, adaptString(next, n)))
        return next;
      while (*next) ++next;
    }
    return 0;
  }
#endif
  char* allocString(size_t n) {
    if (!canAlloc(n)) {
      _overflowed = true;
      return 0;
    }
    char* s = _left;
    _left += n;
    checkInvariants();
    return s;
  }
  template <typename T>
  T* allocRight() {
    return reinterpret_cast<T*>(allocRight(sizeof(T)));
  }
  void* allocRight(size_t bytes) {
    if (!canAlloc(bytes)) {
      _overflowed = true;
      return 0;
    }
    _right -= bytes;
    return _right;
  }
  char *_begin, *_left, *_right, *_end;
  bool _overflowed;
};
template <typename T>
class SerializedValue {
 public:
  explicit SerializedValue(T str) : _str(str) {}
  operator T() const {
    return _str;
  }
  const char* data() const {
    return _str.c_str();
  }
  size_t size() const {
    return _str.length();
  }
 private:
  T _str;
};
template <typename TChar>
class SerializedValue<TChar*> {
 public:
  explicit SerializedValue(TChar* p, size_t n) : _data(p), _size(n) {}
  operator TChar*() const {
    return _data;
  }
  TChar* data() const {
    return _data;
  }
  size_t size() const {
    return _size;
  }
 private:
  TChar* _data;
  size_t _size;
};
template <typename T>
inline SerializedValue<T> serialized(T str) {
  return SerializedValue<T>(str);
}
template <typename TChar>
inline SerializedValue<TChar*> serialized(TChar* p) {
  return SerializedValue<TChar*>(p, adaptString(p).size());
}
template <typename TChar>
inline SerializedValue<TChar*> serialized(TChar* p, size_t n) {
  return SerializedValue<TChar*>(p, n);
}
}  // namespace ARDUINOJSON_NAMESPACE
#if defined(__clang__)
#  pragma clang diagnostic push
#  pragma clang diagnostic ignored "-Wconversion"
#elif defined(__GNUC__)
#  if __GNUC__ > 4 || (__GNUC__ == 4 && __GNUC_MINOR__ >= 6)
#    pragma GCC diagnostic push
#  endif
#  pragma GCC diagnostic ignored "-Wconversion"
#endif
namespace ARDUINOJSON_NAMESPACE {
template <typename TOut, typename TIn>
typename enable_if<is_integral<TIn>::value && is_unsigned<TIn>::value &&
                       is_integral<TOut>::value && sizeof(TOut) <= sizeof(TIn),
                   bool>::type
canConvertNumber(TIn value) {
  return value <= TIn(numeric_limits<TOut>::highest());
}
template <typename TOut, typename TIn>
typename enable_if<is_integral<TIn>::value && is_unsigned<TIn>::value &&
                       is_integral<TOut>::value && sizeof(TIn) < sizeof(TOut),
                   bool>::type
canConvertNumber(TIn) {
  return true;
}
template <typename TOut, typename TIn>
typename enable_if<is_integral<TIn>::value && is_floating_point<TOut>::value,
                   bool>::type
canConvertNumber(TIn) {
  return true;
}
template <typename TOut, typename TIn>
typename enable_if<is_integral<TIn>::value && is_signed<TIn>::value &&
                       is_integral<TOut>::value && is_signed<TOut>::value &&
                       sizeof(TOut) < sizeof(TIn),
                   bool>::type
canConvertNumber(TIn value) {
  return value >= TIn(numeric_limits<TOut>::lowest()) &&
         value <= TIn(numeric_limits<TOut>::highest());
}
template <typename TOut, typename TIn>
typename enable_if<is_integral<TIn>::value && is_signed<TIn>::value &&
                       is_integral<TOut>::value && is_signed<TOut>::value &&
                       sizeof(TIn) <= sizeof(TOut),
                   bool>::type
canConvertNumber(TIn) {
  return true;
}
template <typename TOut, typename TIn>
typename enable_if<is_integral<TIn>::value && is_signed<TIn>::value &&
                       is_integral<TOut>::value && is_unsigned<TOut>::value &&
                       sizeof(TOut) >= sizeof(TIn),
                   bool>::type
canConvertNumber(TIn value) {
  if (value < 0)
    return false;
  return TOut(value) <= numeric_limits<TOut>::highest();
}
template <typename TOut, typename TIn>
typename enable_if<is_integral<TIn>::value && is_signed<TIn>::value &&
                       is_integral<TOut>::value && is_unsigned<TOut>::value &&
                       sizeof(TOut) < sizeof(TIn),
                   bool>::type
canConvertNumber(TIn value) {
  if (value < 0)
    return false;
  return value <= TIn(numeric_limits<TOut>::highest());
}
template <typename TOut, typename TIn>
typename enable_if<is_floating_point<TIn>::value &&
                       !is_floating_point<TOut>::value,
                   bool>::type
canConvertNumber(TIn value) {
  return value >= numeric_limits<TOut>::lowest() &&
         value <= numeric_limits<TOut>::highest();
}
template <typename TOut, typename TIn>
TOut convertNumber(TIn value) {
  return canConvertNumber<TOut>(value) ? TOut(value) : 0;
}
}  // namespace ARDUINOJSON_NAMESPACE
#if defined(__clang__)
#  pragma clang diagnostic pop
#elif defined(__GNUC__)
#  if __GNUC__ > 4 || (__GNUC__ == 4 && __GNUC_MINOR__ >= 6)
#    pragma GCC diagnostic pop
#  endif
#endif
#if defined(__GNUC__)
#  if __GNUC__ >= 7
#    pragma GCC diagnostic push
#    pragma GCC diagnostic ignored "-Wmaybe-uninitialized"
#    pragma GCC diagnostic ignored "-Wuninitialized"
#  endif
#endif
namespace ARDUINOJSON_NAMESPACE {
class VariantData {
  VariantContent _content;  // must be first to allow cast from array to variant
  uint8_t _flags;
 public:
  void init() {
    _flags = VALUE_IS_NULL;
  }
  template <typename TVisitor>
  typename TVisitor::result_type accept(TVisitor &visitor) const {
    switch (type()) {
      case VALUE_IS_FLOAT:
        return visitor.visitFloat(_content.asFloat);
      case VALUE_IS_ARRAY:
        return visitor.visitArray(_content.asCollection);
      case VALUE_IS_OBJECT:
        return visitor.visitObject(_content.asCollection);
      case VALUE_IS_LINKED_STRING:
      case VALUE_IS_OWNED_STRING:
        return visitor.visitString(_content.asString.data,
                                   _content.asString.size);
      case VALUE_IS_OWNED_RAW:
      case VALUE_IS_LINKED_RAW:
        return visitor.visitRawJson(_content.asString.data,
                                    _content.asString.size);
      case VALUE_IS_SIGNED_INTEGER:
        return visitor.visitSignedInteger(_content.asSignedInteger);
      case VALUE_IS_UNSIGNED_INTEGER:
        return visitor.visitUnsignedInteger(_content.asUnsignedInteger);
      case VALUE_IS_BOOLEAN:
        return visitor.visitBoolean(_content.asBoolean != 0);
      default:
        return visitor.visitNull();
    }
  }
  template <typename T>
  T asIntegral() const;
  template <typename T>
  T asFloat() const;
  String asString() const;
  bool asBoolean() const;
  CollectionData *asArray() {
    return isArray() ? &_content.asCollection : 0;
  }
  const CollectionData *asArray() const {
    return const_cast<VariantData *>(this)->asArray();
  }
  CollectionData *asObject() {
    return isObject() ? &_content.asCollection : 0;
  }
  const CollectionData *asObject() const {
    return const_cast<VariantData *>(this)->asObject();
  }
  bool copyFrom(const VariantData &src, MemoryPool *pool);
  bool isArray() const {
    return (_flags & VALUE_IS_ARRAY) != 0;
  }
  bool isBoolean() const {
    return type() == VALUE_IS_BOOLEAN;
  }
  bool isCollection() const {
    return (_flags & COLLECTION_MASK) != 0;
  }
  template <typename T>
  bool isInteger() const {
    switch (type()) {
      case VALUE_IS_UNSIGNED_INTEGER:
        return canConvertNumber<T>(_content.asUnsignedInteger);
      case VALUE_IS_SIGNED_INTEGER:
        return canConvertNumber<T>(_content.asSignedInteger);
      default:
        return false;
    }
  }
  bool isFloat() const {
    return (_flags & NUMBER_BIT) != 0;
  }
  bool isString() const {
    return type() == VALUE_IS_LINKED_STRING || type() == VALUE_IS_OWNED_STRING;
  }
  bool isObject() const {
    return (_flags & VALUE_IS_OBJECT) != 0;
  }
  bool isNull() const {
    return type() == VALUE_IS_NULL;
  }
  bool isEnclosed() const {
    return !isFloat();
  }
  void remove(size_t index) {
    if (isArray())
      _content.asCollection.removeElement(index);
  }
  template <typename TAdaptedString>
  void remove(TAdaptedString key) {
    if (isObject())
      _content.asCollection.removeMember(key);
  }
  void setBoolean(bool value) {
    setType(VALUE_IS_BOOLEAN);
    _content.asBoolean = value;
  }
  void setFloat(Float value) {
    setType(VALUE_IS_FLOAT);
    _content.asFloat = value;
  }
  void setLinkedRaw(SerializedValue<const char *> value) {
    if (value.data()) {
      setType(VALUE_IS_LINKED_RAW);
      _content.asString.data = value.data();
      _content.asString.size = value.size();
    } else {
      setType(VALUE_IS_NULL);
    }
  }
  template <typename T>
  bool storeOwnedRaw(SerializedValue<T> value, MemoryPool *pool) {
    const char *dup = pool->saveString(adaptString(value.data(), value.size()));
    if (dup) {
      setType(VALUE_IS_OWNED_RAW);
      _content.asString.data = dup;
      _content.asString.size = value.size();
      return true;
    } else {
      setType(VALUE_IS_NULL);
      return false;
    }
  }
  template <typename T>
  typename enable_if<is_unsigned<T>::value>::type setInteger(T value) {
    setType(VALUE_IS_UNSIGNED_INTEGER);
    _content.asUnsignedInteger = static_cast<UInt>(value);
  }
  template <typename T>
  typename enable_if<is_signed<T>::value>::type setInteger(T value) {
    setType(VALUE_IS_SIGNED_INTEGER);
    _content.asSignedInteger = value;
  }
  void setNull() {
    setType(VALUE_IS_NULL);
  }
  void setString(String s) {
    ARDUINOJSON_ASSERT(s);
    if (s.isLinked())
      setType(VALUE_IS_LINKED_STRING);
    else
      setType(VALUE_IS_OWNED_STRING);
    _content.asString.data = s.c_str();
    _content.asString.size = s.size();
  }
  CollectionData &toArray() {
    setType(VALUE_IS_ARRAY);
    _content.asCollection.clear();
    return _content.asCollection;
  }
  CollectionData &toObject() {
    setType(VALUE_IS_OBJECT);
    _content.asCollection.clear();
    return _content.asCollection;
  }
  size_t memoryUsage() const {
    switch (type()) {
      case VALUE_IS_OWNED_STRING:
      case VALUE_IS_OWNED_RAW:
        return _content.asString.size + 1;
      case VALUE_IS_OBJECT:
      case VALUE_IS_ARRAY:
        return _content.asCollection.memoryUsage();
      default:
        return 0;
    }
  }
  size_t nesting() const {
    return isCollection() ? _content.asCollection.nesting() : 0;
  }
  size_t size() const {
    return isCollection() ? _content.asCollection.size() : 0;
  }
  VariantData *addElement(MemoryPool *pool) {
    if (isNull())
      toArray();
    if (!isArray())
      return 0;
    return _content.asCollection.addElement(pool);
  }
  VariantData *getElement(size_t index) const {
    return isArray() ? _content.asCollection.getElement(index) : 0;
  }
  VariantData *getOrAddElement(size_t index, MemoryPool *pool) {
    if (isNull())
      toArray();
    if (!isArray())
      return 0;
    return _content.asCollection.getOrAddElement(index, pool);
  }
  template <typename TAdaptedString>
  VariantData *getMember(TAdaptedString key) const {
    return isObject() ? _content.asCollection.getMember(key) : 0;
  }
  template <typename TAdaptedString, typename TStoragePolicy>
  VariantData *getOrAddMember(TAdaptedString key, MemoryPool *pool,
                              TStoragePolicy storage_policy) {
    if (isNull())
      toObject();
    if (!isObject())
      return 0;
    return _content.asCollection.getOrAddMember(key, pool, storage_policy);
  }
  void movePointers(ptrdiff_t stringDistance, ptrdiff_t variantDistance) {
    if (_flags & OWNED_VALUE_BIT)
      _content.asString.data += stringDistance;
    if (_flags & COLLECTION_MASK)
      _content.asCollection.movePointers(stringDistance, variantDistance);
  }
  uint8_t type() const {
    return _flags & VALUE_MASK;
  }
  template <typename TAdaptedString, typename TStoragePolicy>
  inline bool storeString(TAdaptedString value, MemoryPool *pool,
                          TStoragePolicy storage) {
    if (value.isNull()) {
      setNull();
      return true;
    }
    return storage.store(value, pool, VariantStringSetter(this));
  }
 private:
  void setType(uint8_t t) {
    _flags &= OWNED_KEY_BIT;
    _flags |= t;
  }
  struct VariantStringSetter {
    VariantStringSetter(VariantData *instance) : _instance(instance) {}
    template <typename TStoredString>
    void operator()(TStoredString s) {
      if (s)
        _instance->setString(s);
      else
        _instance->setNull();
    }
    VariantData *_instance;
  };
};
}  // namespace ARDUINOJSON_NAMESPACE
#if defined(__GNUC__)
#  if __GNUC__ >= 8
#    pragma GCC diagnostic pop
#  endif
#endif
namespace ARDUINOJSON_NAMESPACE {
struct SlotKeySetter {
  SlotKeySetter(VariantSlot* instance) : _instance(instance) {}
  template <typename TStoredString>
  void operator()(TStoredString s) {
    if (!s)
      return;
    ARDUINOJSON_ASSERT(_instance != 0);
    _instance->setKey(s);
  }
  VariantSlot* _instance;
};
template <typename TAdaptedString, typename TStoragePolicy>
inline bool slotSetKey(VariantSlot* var, TAdaptedString key, MemoryPool* pool,
                       TStoragePolicy storage) {
  if (!var)
    return false;
  return storage.store(key, pool, SlotKeySetter(var));
}
inline size_t slotSize(const VariantSlot* var) {
  size_t n = 0;
  while (var) {
    n++;
    var = var->next();
  }
  return n;
}
inline VariantData* slotData(VariantSlot* slot) {
  return reinterpret_cast<VariantData*>(slot);
}
struct Visitable {
};
template <typename T>
struct IsVisitable : is_base_of<Visitable, T> {};
template <typename T>
struct IsVisitable<T &> : IsVisitable<T> {};
template <typename T, typename Enable = void>
struct Converter;
template <typename T1, typename T2>
class InvalidConversion;  // Error here? See https://arduinojson.org/v6/invalid-conversion/
}  // namespace ARDUINOJSON_NAMESPACE
#ifdef _MSC_VER  // Visual Studio
#  define FORCE_INLINE  // __forceinline causes C4714 when returning std::string
#  define NO_INLINE __declspec(noinline)
#  ifndef ARDUINOJSON_DEPRECATED
#    define ARDUINOJSON_DEPRECATED(msg) __declspec(deprecated(msg))
#  endif
#elif defined(__GNUC__)  // GCC or Clang
#  define FORCE_INLINE __attribute__((always_inline))
#  define NO_INLINE __attribute__((noinline))
#  ifndef ARDUINOJSON_DEPRECATED
#    if __GNUC__ > 4 || (__GNUC__ == 4 && __GNUC_MINOR__ >= 5)
#      define ARDUINOJSON_DEPRECATED(msg) __attribute__((deprecated(msg)))
#    else
#      define ARDUINOJSON_DEPRECATED(msg) __attribute__((deprecated))
#    endif
#  endif
#else  // Other compilers
#  define FORCE_INLINE
#  define NO_INLINE
#  ifndef ARDUINOJSON_DEPRECATED
#    define ARDUINOJSON_DEPRECATED(msg)
#  endif
#endif
#if __cplusplus >= 201103L
#  define NOEXCEPT noexcept
#else
#  define NOEXCEPT throw()
#endif
#if defined(__has_attribute)
#  if __has_attribute(no_sanitize)
#    define ARDUINOJSON_NO_SANITIZE(check) __attribute__((no_sanitize(check)))
#  else
#    define ARDUINOJSON_NO_SANITIZE(check)
#  endif
#else
#  define ARDUINOJSON_NO_SANITIZE(check)
#endif
namespace ARDUINOJSON_NAMESPACE {
struct LinkStringStoragePolicy {
  template <typename TAdaptedString, typename TCallback>
  bool store(TAdaptedString str, MemoryPool *, TCallback callback) {
    String storedString(str.data(), str.size(), String::Linked);
    callback(storedString);
    return !str.isNull();
  }
};
struct CopyStringStoragePolicy {
  template <typename TAdaptedString, typename TCallback>
  bool store(TAdaptedString str, MemoryPool *pool, TCallback callback);
};
class LinkOrCopyStringStoragePolicy : LinkStringStoragePolicy,
                                      CopyStringStoragePolicy {
 public:
  LinkOrCopyStringStoragePolicy(bool link) : _link(link) {}
  template <typename TAdaptedString, typename TCallback>
  bool store(TAdaptedString str, MemoryPool *pool, TCallback callback) {
    if (_link)
      return LinkStringStoragePolicy::store(str, pool, callback);
    else
      return CopyStringStoragePolicy::store(str, pool, callback);
  }
 private:
  bool _link;
};
template <typename T>
inline CopyStringStoragePolicy getStringStoragePolicy(const T &) {
  return CopyStringStoragePolicy();
}
inline LinkStringStoragePolicy getStringStoragePolicy(const char *) {
  return LinkStringStoragePolicy();
}
inline LinkOrCopyStringStoragePolicy getStringStoragePolicy(const String &s) {
  return LinkOrCopyStringStoragePolicy(s.isLinked());
}
template <typename TVisitor>
inline typename TVisitor::result_type variantAccept(const VariantData *var,
                                                    TVisitor &visitor) {
  if (var != 0)
    return var->accept(visitor);
  else
    return visitor.visitNull();
}
inline const CollectionData *variantAsArray(const VariantData *var) {
  return var != 0 ? var->asArray() : 0;
}
inline const CollectionData *variantAsObject(const VariantData *var) {
  return var != 0 ? var->asObject() : 0;
}
inline CollectionData *variantAsObject(VariantData *var) {
  return var != 0 ? var->asObject() : 0;
}
inline bool variantCopyFrom(VariantData *dst, const VariantData *src,
                            MemoryPool *pool) {
  if (!dst)
    return false;
  if (!src) {
    dst->setNull();
    return true;
  }
  return dst->copyFrom(*src, pool);
}
inline int variantCompare(const VariantData *a, const VariantData *b);
inline void variantSetNull(VariantData *var) {
  if (!var)
    return;
  var->setNull();
}
template <typename TAdaptedString, typename TStoragePolicy>
inline bool variantSetString(VariantData *var, TAdaptedString value,
                             MemoryPool *pool, TStoragePolicy storage_policy) {
  return var != 0 ? var->storeString(value, pool, storage_policy) : 0;
}
inline size_t variantSize(const VariantData *var) {
  return var != 0 ? var->size() : 0;
}
inline CollectionData *variantToArray(VariantData *var) {
  if (!var)
    return 0;
  return &var->toArray();
}
inline CollectionData *variantToObject(VariantData *var) {
  if (!var)
    return 0;
  return &var->toObject();
}
inline NO_INLINE VariantData *variantAddElement(VariantData *var,
                                                MemoryPool *pool) {
  return var != 0 ? var->addElement(pool) : 0;
}
inline NO_INLINE VariantData *variantGetOrAddElement(VariantData *var,
                                                     size_t index,
                                                     MemoryPool *pool) {
  return var != 0 ? var->getOrAddElement(index, pool) : 0;
}
template <typename TChar>
NO_INLINE VariantData *variantGetOrAddMember(VariantData *var, TChar *key,
                                             MemoryPool *pool) {
  if (!var)
    return 0;
  return var->getOrAddMember(adaptString(key), pool,
                             getStringStoragePolicy(key));
}
template <typename TString>
NO_INLINE VariantData *variantGetOrAddMember(VariantData *var,
                                             const TString &key,
                                             MemoryPool *pool) {
  if (!var)
    return 0;
  return var->getOrAddMember(adaptString(key), pool,
                             getStringStoragePolicy(key));
}
inline bool variantIsNull(const VariantData *var) {
  return var == 0 || var->isNull();
}
enum CompareResult {
  COMPARE_RESULT_DIFFER = 0,
  COMPARE_RESULT_EQUAL = 1,
  COMPARE_RESULT_GREATER = 2,
  COMPARE_RESULT_LESS = 4,
  COMPARE_RESULT_GREATER_OR_EQUAL = 3,
  COMPARE_RESULT_LESS_OR_EQUAL = 5
};
template <typename T>
CompareResult arithmeticCompare(const T &lhs, const T &rhs) {
  if (lhs < rhs)
    return COMPARE_RESULT_LESS;
  else if (lhs > rhs)
    return COMPARE_RESULT_GREATER;
  else
    return COMPARE_RESULT_EQUAL;
}
template <typename T1, typename T2>
CompareResult arithmeticCompare(
    const T1 &lhs, const T2 &rhs,
    typename enable_if<is_integral<T1>::value && is_integral<T2>::value &&
                           sizeof(T1) < sizeof(T2),
                       int  // Using int instead of void to avoid C2572 on
                       >::type * = 0) {
  return arithmeticCompare<T2>(static_cast<T2>(lhs), rhs);
}
template <typename T1, typename T2>
CompareResult arithmeticCompare(
    const T1 &lhs, const T2 &rhs,
    typename enable_if<is_integral<T1>::value && is_integral<T2>::value &&
                       sizeof(T2) < sizeof(T1)>::type * = 0) {
  return arithmeticCompare<T1>(lhs, static_cast<T1>(rhs));
}
template <typename T1, typename T2>
CompareResult arithmeticCompare(
    const T1 &lhs, const T2 &rhs,
    typename enable_if<is_integral<T1>::value && is_integral<T2>::value &&
                       is_signed<T1>::value == is_signed<T2>::value &&
                       sizeof(T2) == sizeof(T1)>::type * = 0) {
  return arithmeticCompare<T1>(lhs, static_cast<T1>(rhs));
}
template <typename T1, typename T2>
CompareResult arithmeticCompare(
    const T1 &lhs, const T2 &rhs,
    typename enable_if<is_integral<T1>::value && is_integral<T2>::value &&
                       is_unsigned<T1>::value && is_signed<T2>::value &&
                       sizeof(T2) == sizeof(T1)>::type * = 0) {
  if (rhs < 0)
    return COMPARE_RESULT_GREATER;
  return arithmeticCompare<T1>(lhs, static_cast<T1>(rhs));
}
template <typename T1, typename T2>
CompareResult arithmeticCompare(
    const T1 &lhs, const T2 &rhs,
    typename enable_if<is_integral<T1>::value && is_integral<T2>::value &&
                       is_signed<T1>::value && is_unsigned<T2>::value &&
                       sizeof(T2) == sizeof(T1)>::type * = 0) {
  if (lhs < 0)
    return COMPARE_RESULT_LESS;
  return arithmeticCompare<T2>(static_cast<T2>(lhs), rhs);
}
template <typename T1, typename T2>
CompareResult arithmeticCompare(
    const T1 &lhs, const T2 &rhs,
    typename enable_if<is_floating_point<T1>::value ||
                       is_floating_point<T2>::value>::type * = 0) {
  return arithmeticCompare<double>(static_cast<double>(lhs),
                                   static_cast<double>(rhs));
}
template <typename T2>
CompareResult arithmeticCompareNegateLeft(
    UInt, const T2 &, typename enable_if<is_unsigned<T2>::value>::type * = 0) {
  return COMPARE_RESULT_LESS;
}
template <typename T2>
CompareResult arithmeticCompareNegateLeft(
    UInt lhs, const T2 &rhs,
    typename enable_if<is_signed<T2>::value>::type * = 0) {
  if (rhs > 0)
    return COMPARE_RESULT_LESS;
  return arithmeticCompare(-rhs, static_cast<T2>(lhs));
}
template <typename T1>
CompareResult arithmeticCompareNegateRight(
    const T1 &, UInt, typename enable_if<is_unsigned<T1>::value>::type * = 0) {
  return COMPARE_RESULT_GREATER;
}
template <typename T1>
CompareResult arithmeticCompareNegateRight(
    const T1 &lhs, UInt rhs,
    typename enable_if<is_signed<T1>::value>::type * = 0) {
  if (lhs > 0)
    return COMPARE_RESULT_GREATER;
  return arithmeticCompare(static_cast<T1>(rhs), -lhs);
}
struct VariantTag {};
template <typename T>
struct IsVariant : is_base_of<VariantTag, T> {};
template <typename T1, typename T2>
CompareResult compare(const T1 &lhs, const T2 &rhs);  // VariantCompare.cpp
template <typename TVariant>
struct VariantOperators {
  template <typename T>
  friend
      typename enable_if<!IsVariant<T>::value && !is_array<T>::value, T>::type
      operator|(const TVariant &variant, const T &defaultValue) {
    if (variant.template is<T>())
      return variant.template as<T>();
    else
      return defaultValue;
  }
  friend const char *operator|(const TVariant &variant,
                               const char *defaultValue) {
    if (variant.template is<const char *>())
      return variant.template as<const char *>();
    else
      return defaultValue;
  }
  template <typename T>
  friend typename enable_if<IsVariant<T>::value, typename T::variant_type>::type
  operator|(const TVariant &variant, T defaultValue) {
    if (variant)
      return variant;
    else
      return defaultValue;
  }
  template <typename T>
  friend bool operator==(T *lhs, TVariant rhs) {
    return compare(rhs, lhs) == COMPARE_RESULT_EQUAL;
  }
  template <typename T>
  friend bool operator==(const T &lhs, TVariant rhs) {
    return compare(rhs, lhs) == COMPARE_RESULT_EQUAL;
  }
  template <typename T>
  friend bool operator==(TVariant lhs, T *rhs) {
    return compare(lhs, rhs) == COMPARE_RESULT_EQUAL;
  }
  template <typename T>
  friend typename enable_if<!IsVisitable<T>::value, bool>::type operator==(
      TVariant lhs, const T &rhs) {
    return compare(lhs, rhs) == COMPARE_RESULT_EQUAL;
  }
  template <typename T>
  friend bool operator!=(T *lhs, TVariant rhs) {
    return compare(rhs, lhs) != COMPARE_RESULT_EQUAL;
  }
  template <typename T>
  friend bool operator!=(const T &lhs, TVariant rhs) {
    return compare(rhs, lhs) != COMPARE_RESULT_EQUAL;
  }
  template <typename T>
  friend bool operator!=(TVariant lhs, T *rhs) {
    return compare(lhs, rhs) != COMPARE_RESULT_EQUAL;
  }
  template <typename T>
  friend typename enable_if<!IsVisitable<T>::value, bool>::type operator!=(
      TVariant lhs, const T &rhs) {
    return compare(lhs, rhs) != COMPARE_RESULT_EQUAL;
  }
  template <typename T>
  friend bool operator<(T *lhs, TVariant rhs) {
    return compare(rhs, lhs) == COMPARE_RESULT_GREATER;
  }
  template <typename T>
  friend bool operator<(const T &lhs, TVariant rhs) {
    return compare(rhs, lhs) == COMPARE_RESULT_GREATER;
  }
  template <typename T>
  friend bool operator<(TVariant lhs, T *rhs) {
    return compare(lhs, rhs) == COMPARE_RESULT_LESS;
  }
  template <typename T>
  friend typename enable_if<!IsVisitable<T>::value, bool>::type operator<(
      TVariant lhs, const T &rhs) {
    return compare(lhs, rhs) == COMPARE_RESULT_LESS;
  }
  template <typename T>
  friend bool operator<=(T *lhs, TVariant rhs) {
    return (compare(rhs, lhs) & COMPARE_RESULT_GREATER_OR_EQUAL) != 0;
  }
  template <typename T>
  friend bool operator<=(const T &lhs, TVariant rhs) {
    return (compare(rhs, lhs) & COMPARE_RESULT_GREATER_OR_EQUAL) != 0;
  }
  template <typename T>
  friend bool operator<=(TVariant lhs, T *rhs) {
    return (compare(lhs, rhs) & COMPARE_RESULT_LESS_OR_EQUAL) != 0;
  }
  template <typename T>
  friend typename enable_if<!IsVisitable<T>::value, bool>::type operator<=(
      TVariant lhs, const T &rhs) {
    return (compare(lhs, rhs) & COMPARE_RESULT_LESS_OR_EQUAL) != 0;
  }
  template <typename T>
  friend bool operator>(T *lhs, TVariant rhs) {
    return compare(rhs, lhs) == COMPARE_RESULT_LESS;
  }
  template <typename T>
  friend bool operator>(const T &lhs, TVariant rhs) {
    return compare(rhs, lhs) == COMPARE_RESULT_LESS;
  }
  template <typename T>
  friend bool operator>(TVariant lhs, T *rhs) {
    return compare(lhs, rhs) == COMPARE_RESULT_GREATER;
  }
  template <typename T>
  friend typename enable_if<!IsVisitable<T>::value, bool>::type operator>(
      TVariant lhs, const T &rhs) {
    return compare(lhs, rhs) == COMPARE_RESULT_GREATER;
  }
  template <typename T>
  friend bool operator>=(T *lhs, TVariant rhs) {
    return (compare(rhs, lhs) & COMPARE_RESULT_LESS_OR_EQUAL) != 0;
  }
  template <typename T>
  friend bool operator>=(const T &lhs, TVariant rhs) {
    return (compare(rhs, lhs) & COMPARE_RESULT_LESS_OR_EQUAL) != 0;
  }
  template <typename T>
  friend bool operator>=(TVariant lhs, T *rhs) {
    return (compare(lhs, rhs) & COMPARE_RESULT_GREATER_OR_EQUAL) != 0;
  }
  template <typename T>
  friend typename enable_if<!IsVisitable<T>::value, bool>::type operator>=(
      TVariant lhs, const T &rhs) {
    return (compare(lhs, rhs) & COMPARE_RESULT_GREATER_OR_EQUAL) != 0;
  }
};
class ArrayRef;
class ObjectRef;
template <typename>
class ElementProxy;
template <typename TArray>
class ArrayShortcuts {
 public:
  FORCE_INLINE ElementProxy<TArray> operator[](size_t index) const;
  FORCE_INLINE ObjectRef createNestedObject() const;
  FORCE_INLINE ArrayRef createNestedArray() const;
  template <typename T>
  FORCE_INLINE bool add(const T &value) const {
    return impl()->addElement().set(value);
  }
  template <typename T>
  FORCE_INLINE bool add(T *value) const {
    return impl()->addElement().set(value);
  }
 private:
  const TArray *impl() const {
    return static_cast<const TArray *>(this);
  }
};
template <typename TParent, typename TStringRef>
class MemberProxy;
template <typename TObject>
class ObjectShortcuts {
 public:
  template <typename TString>
  FORCE_INLINE typename enable_if<IsString<TString>::value, bool>::type
  containsKey(const TString &key) const;
  template <typename TChar>
  FORCE_INLINE typename enable_if<IsString<TChar *>::value, bool>::type
  containsKey(TChar *key) const;
  template <typename TString>
  FORCE_INLINE typename enable_if<IsString<TString>::value,
                                  MemberProxy<TObject, TString> >::type
  operator[](const TString &key) const;
  template <typename TChar>
  FORCE_INLINE typename enable_if<IsString<TChar *>::value,
                                  MemberProxy<TObject, TChar *> >::type
  operator[](TChar *key) const;
  template <typename TString>
  FORCE_INLINE ArrayRef createNestedArray(const TString &key) const;
  template <typename TChar>
  FORCE_INLINE ArrayRef createNestedArray(TChar *key) const;
  template <typename TString>
  ObjectRef createNestedObject(const TString &key) const;
  template <typename TChar>
  ObjectRef createNestedObject(TChar *key) const;
 private:
  const TObject *impl() const {
    return static_cast<const TObject *>(this);
  }
};
template <typename TVariant>
class VariantShortcuts : public ObjectShortcuts<TVariant>,
                         public ArrayShortcuts<TVariant> {
 public:
  using ArrayShortcuts<TVariant>::createNestedArray;
  using ArrayShortcuts<TVariant>::createNestedObject;
  using ArrayShortcuts<TVariant>::operator[];
  using ObjectShortcuts<TVariant>::createNestedArray;
  using ObjectShortcuts<TVariant>::createNestedObject;
  using ObjectShortcuts<TVariant>::operator[];
};
class ArrayRef;
class ObjectRef;
template <typename TData>
class VariantRefBase : public VariantTag {
 public:
  FORCE_INLINE bool isNull() const {
    return variantIsNull(_data);
  }
  FORCE_INLINE bool isUnbound() const {
    return !_data;
  }
  FORCE_INLINE size_t memoryUsage() const {
    return _data ? _data->memoryUsage() : 0;
  }
  FORCE_INLINE size_t nesting() const {
    return _data ? _data->nesting() : 0;
  }
  size_t size() const {
    return variantSize(_data);
  }
 protected:
  VariantRefBase(TData *data) : _data(data) {}
  TData *_data;
  friend TData *getData(const VariantRefBase &variant) {
    return variant._data;
  }
};
class VariantRef : public VariantRefBase<VariantData>,
                   public VariantOperators<VariantRef>,
                   public VariantShortcuts<VariantRef>,
                   public Visitable {
  typedef VariantRefBase<VariantData> base_type;
  friend class VariantConstRef;
 public:
  FORCE_INLINE VariantRef(MemoryPool *pool, VariantData *data)
      : base_type(data), _pool(pool) {}
  FORCE_INLINE VariantRef() : base_type(0), _pool(0) {}
  FORCE_INLINE void clear() const {
    return variantSetNull(_data);
  }
  template <typename T>
  FORCE_INLINE bool set(const T &value) const {
    Converter<T>::toJson(value, *this);
    return _pool && !_pool->overflowed();
  }
  bool ARDUINOJSON_DEPRECATED(
      "Support for char is deprecated, use int8_t or uint8_t instead")
      set(char value) const;
  template <typename T>
  FORCE_INLINE bool set(T *value) const {
    Converter<T *>::toJson(value, *this);
    return _pool && !_pool->overflowed();
  }
  template <typename T>
  FORCE_INLINE
      typename enable_if<!is_same<T, char *>::value && !is_same<T, char>::value,
                         T>::type
      as() const {
    return Converter<T>::fromJson(*this);
  }
  template <typename T>
  FORCE_INLINE typename enable_if<is_same<T, char *>::value, const char *>::type
  ARDUINOJSON_DEPRECATED("Replace as<char*>() with as<const char*>()")
      as() const {
    return as<const char *>();
  }
  template <typename T>
  FORCE_INLINE typename enable_if<is_same<T, char>::value, char>::type
  ARDUINOJSON_DEPRECATED(
      "Support for char is deprecated, use int8_t or uint8_t instead")
      as() const {
    return static_cast<char>(as<signed char>());
  }
  template <typename T>
  FORCE_INLINE
      typename enable_if<!is_same<T, char *>::value && !is_same<T, char>::value,
                         bool>::type
      is() const {
    return Converter<T>::checkJson(*this);
  }
  template <typename T>
  FORCE_INLINE typename enable_if<is_same<T, char *>::value, bool>::type
  ARDUINOJSON_DEPRECATED("Replace is<char*>() with is<const char*>()")
      is() const {
    return is<const char *>();
  }
  template <typename T>
  FORCE_INLINE typename enable_if<is_same<T, char>::value, bool>::type
  ARDUINOJSON_DEPRECATED(
      "Support for char is deprecated, use int8_t or uint8_t instead")
      is() const {
    return is<signed char>();
  }
  template <typename T>
  FORCE_INLINE operator T() const {
    return as<T>();
  }
  template <typename TVisitor>
  typename TVisitor::result_type accept(TVisitor &visitor) const {
    return variantAccept(_data, visitor);
  }
  template <typename T>
  typename enable_if<is_same<T, ArrayRef>::value, ArrayRef>::type to() const;
  template <typename T>
  typename enable_if<is_same<T, ObjectRef>::value, ObjectRef>::type to() const;
  template <typename T>
  typename enable_if<is_same<T, VariantRef>::value, VariantRef>::type to()
      const;
  VariantRef addElement() const;
  FORCE_INLINE VariantRef getElement(size_t) const;
  FORCE_INLINE VariantRef getOrAddElement(size_t) const;
  template <typename TChar>
  FORCE_INLINE VariantRef getMember(TChar *) const;
  template <typename TString>
  FORCE_INLINE typename enable_if<IsString<TString>::value, VariantRef>::type
  getMember(const TString &) const;
  template <typename TChar>
  FORCE_INLINE VariantRef getOrAddMember(TChar *) const;
  template <typename TString>
  FORCE_INLINE VariantRef getOrAddMember(const TString &) const;
  FORCE_INLINE void remove(size_t index) const {
    if (_data)
      _data->remove(index);
  }
  template <typename TChar>
  FORCE_INLINE typename enable_if<IsString<TChar *>::value>::type remove(
      TChar *key) const {
    if (_data)
      _data->remove(adaptString(key));
  }
  template <typename TString>
  FORCE_INLINE typename enable_if<IsString<TString>::value>::type remove(
      const TString &key) const {
    if (_data)
      _data->remove(adaptString(key));
  }
 private:
  MemoryPool *_pool;
  friend MemoryPool *getPool(const VariantRef &variant) {
    return variant._pool;
  }
};
class VariantConstRef : public VariantRefBase<const VariantData>,
                        public VariantOperators<VariantConstRef>,
                        public VariantShortcuts<VariantConstRef>,
                        public Visitable {
  typedef VariantRefBase<const VariantData> base_type;
  friend class VariantRef;
 public:
  VariantConstRef() : base_type(0) {}
  VariantConstRef(const VariantData *data) : base_type(data) {}
  VariantConstRef(VariantRef var) : base_type(var._data) {}
  template <typename TVisitor>
  typename TVisitor::result_type accept(TVisitor &visitor) const {
    return variantAccept(_data, visitor);
  }
  template <typename T>
  FORCE_INLINE
      typename enable_if<!is_same<T, char *>::value && !is_same<T, char>::value,
                         T>::type
      as() const {
    return Converter<T>::fromJson(*this);
  }
  template <typename T>
  FORCE_INLINE typename enable_if<is_same<T, char *>::value, const char *>::type
  ARDUINOJSON_DEPRECATED("Replace as<char*>() with as<const char*>()")
      as() const {
    return as<const char *>();
  }
  template <typename T>
  FORCE_INLINE typename enable_if<is_same<T, char>::value, char>::type
  ARDUINOJSON_DEPRECATED(
      "Support for char is deprecated, use int8_t or uint8_t instead")
      as() const {
    return static_cast<char>(as<signed char>());
  }
  template <typename T>
  FORCE_INLINE
      typename enable_if<!is_same<T, char *>::value && !is_same<T, char>::value,
                         bool>::type
      is() const {
    return Converter<T>::checkJson(*this);
  }
  template <typename T>
  FORCE_INLINE typename enable_if<is_same<T, char *>::value, bool>::type
  ARDUINOJSON_DEPRECATED("Replace is<char*>() with is<const char*>()")
      is() const {
    return is<const char *>();
  }
  template <typename T>
  FORCE_INLINE typename enable_if<is_same<T, char>::value, bool>::type
  ARDUINOJSON_DEPRECATED(
      "Support for char is deprecated, use int8_t or uint8_t instead")
      is() const {
    return is<signed char>();
  }
  template <typename T>
  FORCE_INLINE operator T() const {
    return as<T>();
  }
  FORCE_INLINE VariantConstRef getElement(size_t) const;
  FORCE_INLINE VariantConstRef operator[](size_t index) const {
    return getElement(index);
  }
  template <typename TString>
  FORCE_INLINE VariantConstRef getMember(const TString &key) const {
    return VariantConstRef(
        objectGetMember(variantAsObject(_data), adaptString(key)));
  }
  template <typename TChar>
  FORCE_INLINE VariantConstRef getMember(TChar *key) const {
    const CollectionData *obj = variantAsObject(_data);
    return VariantConstRef(obj ? obj->getMember(adaptString(key)) : 0);
  }
  template <typename TString>
  FORCE_INLINE
      typename enable_if<IsString<TString>::value, VariantConstRef>::type
      operator[](const TString &key) const {
    return getMember(key);
  }
  template <typename TChar>
  FORCE_INLINE
      typename enable_if<IsString<TChar *>::value, VariantConstRef>::type
      operator[](TChar *key) const {
    return getMember(key);
  }
};
template <>
struct Converter<VariantRef> {
  static void toJson(VariantRef src, VariantRef dst) {
    variantCopyFrom(getData(dst), getData(src), getPool(dst));
  }
  static VariantRef fromJson(VariantRef src) {
    return src;
  }
  static InvalidConversion<VariantConstRef, VariantRef> fromJson(
      VariantConstRef);
  static bool checkJson(VariantRef src) {
    VariantData *data = getData(src);
    return !!data;
  }
  static bool checkJson(VariantConstRef) {
    return false;
  }
};
template <>
struct Converter<VariantConstRef> {
  static void toJson(VariantConstRef src, VariantRef dst) {
    variantCopyFrom(getData(dst), getData(src), getPool(dst));
  }
  static VariantConstRef fromJson(VariantConstRef src) {
    return VariantConstRef(getData(src));
  }
  static bool checkJson(VariantConstRef src) {
    const VariantData *data = getData(src);
    return !!data;
  }
};
class VariantPtr {
 public:
  VariantPtr(MemoryPool *pool, VariantData *data) : _variant(pool, data) {}
  VariantRef *operator->() {
    return &_variant;
  }
  VariantRef &operator*() {
    return _variant;
  }
 private:
  VariantRef _variant;
};
class ArrayIterator {
 public:
  ArrayIterator() : _slot(0) {}
  explicit ArrayIterator(MemoryPool *pool, VariantSlot *slot)
      : _pool(pool), _slot(slot) {}
  VariantRef operator*() const {
    return VariantRef(_pool, _slot->data());
  }
  VariantPtr operator->() {
    return VariantPtr(_pool, _slot->data());
  }
  bool operator==(const ArrayIterator &other) const {
    return _slot == other._slot;
  }
  bool operator!=(const ArrayIterator &other) const {
    return _slot != other._slot;
  }
  ArrayIterator &operator++() {
    _slot = _slot->next();
    return *this;
  }
  ArrayIterator &operator+=(size_t distance) {
    _slot = _slot->next(distance);
    return *this;
  }
  VariantSlot *internal() {
    return _slot;
  }
 private:
  MemoryPool *_pool;
  VariantSlot *_slot;
};
class VariantConstPtr {
 public:
  VariantConstPtr(const VariantData *data) : _variant(data) {}
  VariantConstRef *operator->() {
    return &_variant;
  }
  VariantConstRef &operator*() {
    return _variant;
  }
 private:
  VariantConstRef _variant;
};
class ArrayConstRefIterator {
 public:
  ArrayConstRefIterator() : _slot(0) {}
  explicit ArrayConstRefIterator(const VariantSlot *slot) : _slot(slot) {}
  VariantConstRef operator*() const {
    return VariantConstRef(_slot->data());
  }
  VariantConstPtr operator->() {
    return VariantConstPtr(_slot->data());
  }
  bool operator==(const ArrayConstRefIterator &other) const {
    return _slot == other._slot;
  }
  bool operator!=(const ArrayConstRefIterator &other) const {
    return _slot != other._slot;
  }
  ArrayConstRefIterator &operator++() {
    _slot = _slot->next();
    return *this;
  }
  ArrayConstRefIterator &operator+=(size_t distance) {
    _slot = _slot->next(distance);
    return *this;
  }
  const VariantSlot *internal() {
    return _slot;
  }
 private:
  const VariantSlot *_slot;
};
}  // namespace ARDUINOJSON_NAMESPACE
#define JSON_ARRAY_SIZE(NUMBER_OF_ELEMENTS) \
  ((NUMBER_OF_ELEMENTS) * sizeof(ARDUINOJSON_NAMESPACE::VariantSlot))
namespace ARDUINOJSON_NAMESPACE {
class ObjectRef;
template <typename>
class ElementProxy;
template <typename TData>
class ArrayRefBase {
 public:
  operator VariantConstRef() const {
    const void* data = _data;  // prevent warning cast-align
    return VariantConstRef(reinterpret_cast<const VariantData*>(data));
  }
  template <typename TVisitor>
  FORCE_INLINE typename TVisitor::result_type accept(TVisitor& visitor) const {
    return arrayAccept(_data, visitor);
  }
  FORCE_INLINE bool isNull() const {
    return _data == 0;
  }
  FORCE_INLINE operator bool() const {
    return _data != 0;
  }
  FORCE_INLINE size_t memoryUsage() const {
    return _data ? _data->memoryUsage() : 0;
  }
  FORCE_INLINE size_t nesting() const {
    return _data ? _data->nesting() : 0;
  }
  FORCE_INLINE size_t size() const {
    return _data ? _data->size() : 0;
  }
 protected:
  ArrayRefBase(TData* data) : _data(data) {}
  TData* _data;
};
class ArrayConstRef : public ArrayRefBase<const CollectionData>,
                      public Visitable {
  friend class ArrayRef;
  typedef ArrayRefBase<const CollectionData> base_type;
 public:
  typedef ArrayConstRefIterator iterator;
  FORCE_INLINE iterator begin() const {
    if (!_data)
      return iterator();
    return iterator(_data->head());
  }
  FORCE_INLINE iterator end() const {
    return iterator();
  }
  FORCE_INLINE ArrayConstRef() : base_type(0) {}
  FORCE_INLINE ArrayConstRef(const CollectionData* data) : base_type(data) {}
  FORCE_INLINE bool operator==(ArrayConstRef rhs) const {
    return arrayEquals(_data, rhs._data);
  }
  FORCE_INLINE VariantConstRef operator[](size_t index) const {
    return getElement(index);
  }
  FORCE_INLINE VariantConstRef getElement(size_t index) const {
    return VariantConstRef(_data ? _data->getElement(index) : 0);
  }
};
class ArrayRef : public ArrayRefBase<CollectionData>,
                 public ArrayShortcuts<ArrayRef>,
                 public Visitable {
  typedef ArrayRefBase<CollectionData> base_type;
 public:
  typedef ArrayIterator iterator;
  FORCE_INLINE ArrayRef() : base_type(0), _pool(0) {}
  FORCE_INLINE ArrayRef(MemoryPool* pool, CollectionData* data)
      : base_type(data), _pool(pool) {}
  operator VariantRef() {
    void* data = _data;  // prevent warning cast-align
    return VariantRef(_pool, reinterpret_cast<VariantData*>(data));
  }
  operator ArrayConstRef() const {
    return ArrayConstRef(_data);
  }
  VariantRef addElement() const {
    return VariantRef(_pool, arrayAdd(_data, _pool));
  }
  FORCE_INLINE iterator begin() const {
    if (!_data)
      return iterator();
    return iterator(_pool, _data->head());
  }
  FORCE_INLINE iterator end() const {
    return iterator();
  }
  FORCE_INLINE bool set(ArrayConstRef src) const {
    if (!_data || !src._data)
      return false;
    return _data->copyFrom(*src._data, _pool);
  }
  FORCE_INLINE bool operator==(ArrayRef rhs) const {
    return arrayEquals(_data, rhs._data);
  }
  FORCE_INLINE VariantRef getOrAddElement(size_t index) const {
    return VariantRef(_pool, _data ? _data->getOrAddElement(index, _pool) : 0);
  }
  FORCE_INLINE VariantRef getElement(size_t index) const {
    return VariantRef(_pool, _data ? _data->getElement(index) : 0);
  }
  FORCE_INLINE void remove(iterator it) const {
    if (!_data)
      return;
    _data->removeSlot(it.internal());
  }
  FORCE_INLINE void remove(size_t index) const {
    if (!_data)
      return;
    _data->removeElement(index);
  }
  void clear() const {
    if (!_data)
      return;
    _data->clear();
  }
 private:
  MemoryPool* _pool;
};
template <>
struct Converter<ArrayConstRef> {
  static void toJson(VariantConstRef src, VariantRef dst) {
    variantCopyFrom(getData(dst), getData(src), getPool(dst));
  }
  static ArrayConstRef fromJson(VariantConstRef src) {
    return ArrayConstRef(variantAsArray(getData(src)));
  }
  static bool checkJson(VariantConstRef src) {
    const VariantData* data = getData(src);
    return data && data->isArray();
  }
};
template <>
struct Converter<ArrayRef> {
  static void toJson(VariantConstRef src, VariantRef dst) {
    variantCopyFrom(getData(dst), getData(src), getPool(dst));
  }
  static ArrayRef fromJson(VariantRef src) {
    VariantData* data = getData(src);
    MemoryPool* pool = getPool(src);
    return ArrayRef(pool, data != 0 ? data->asArray() : 0);
  }
  static InvalidConversion<VariantConstRef, ArrayRef> fromJson(VariantConstRef);
  static bool checkJson(VariantConstRef) {
    return false;
  }
  static bool checkJson(VariantRef src) {
    VariantData* data = getData(src);
    return data && data->isArray();
  }
};
template <typename TVisitor>
typename TVisitor::result_type objectAccept(const CollectionData *obj,
                                            TVisitor &visitor) {
  if (obj)
    return visitor.visitObject(*obj);
  else
    return visitor.visitNull();
}
inline bool objectEquals(const CollectionData *lhs, const CollectionData *rhs) {
  if (lhs == rhs)
    return true;
  if (!lhs || !rhs)
    return false;
  return lhs->equalsObject(*rhs);
}
template <typename TAdaptedString>
inline VariantData *objectGetMember(const CollectionData *obj,
                                    TAdaptedString key) {
  if (!obj)
    return 0;
  return obj->getMember(key);
}
template <typename TAdaptedString>
void objectRemove(CollectionData *obj, TAdaptedString key) {
  if (!obj)
    return;
  obj->removeMember(key);
}
template <typename TAdaptedString, typename TStoragePolicy>
inline VariantData *objectGetOrAddMember(CollectionData *obj,
                                         TAdaptedString key, MemoryPool *pool,
                                         TStoragePolicy storage_policy) {
  if (!obj)
    return 0;
  return obj->getOrAddMember(key, pool, storage_policy);
}
class Pair {
 public:
  Pair(MemoryPool* pool, VariantSlot* slot) {
    if (slot) {
      _key = String(slot->key(),
                    slot->ownsKey() ? String::Copied : String::Linked);
      _value = VariantRef(pool, slot->data());
    }
  }
  String key() const {
    return _key;
  }
  VariantRef value() const {
    return _value;
  }
 private:
  String _key;
  VariantRef _value;
};
class PairConst {
 public:
  PairConst(const VariantSlot* slot) {
    if (slot) {
      _key = String(slot->key(),
                    slot->ownsKey() ? String::Copied : String::Linked);
      _value = VariantConstRef(slot->data());
    }
  }
  String key() const {
    return _key;
  }
  VariantConstRef value() const {
    return _value;
  }
 private:
  String _key;
  VariantConstRef _value;
};
class PairPtr {
 public:
  PairPtr(MemoryPool *pool, VariantSlot *slot) : _pair(pool, slot) {}
  const Pair *operator->() const {
    return &_pair;
  }
  const Pair &operator*() const {
    return _pair;
  }
 private:
  Pair _pair;
};
class ObjectIterator {
 public:
  ObjectIterator() : _slot(0) {}
  explicit ObjectIterator(MemoryPool *pool, VariantSlot *slot)
      : _pool(pool), _slot(slot) {}
  Pair operator*() const {
    return Pair(_pool, _slot);
  }
  PairPtr operator->() {
    return PairPtr(_pool, _slot);
  }
  bool operator==(const ObjectIterator &other) const {
    return _slot == other._slot;
  }
  bool operator!=(const ObjectIterator &other) const {
    return _slot != other._slot;
  }
  ObjectIterator &operator++() {
    _slot = _slot->next();
    return *this;
  }
  ObjectIterator &operator+=(size_t distance) {
    _slot = _slot->next(distance);
    return *this;
  }
  VariantSlot *internal() {
    return _slot;
  }
 private:
  MemoryPool *_pool;
  VariantSlot *_slot;
};
class PairConstPtr {
 public:
  PairConstPtr(const VariantSlot *slot) : _pair(slot) {}
  const PairConst *operator->() const {
    return &_pair;
  }
  const PairConst &operator*() const {
    return _pair;
  }
 private:
  PairConst _pair;
};
class ObjectConstIterator {
 public:
  ObjectConstIterator() : _slot(0) {}
  explicit ObjectConstIterator(const VariantSlot *slot) : _slot(slot) {}
  PairConst operator*() const {
    return PairConst(_slot);
  }
  PairConstPtr operator->() {
    return PairConstPtr(_slot);
  }
  bool operator==(const ObjectConstIterator &other) const {
    return _slot == other._slot;
  }
  bool operator!=(const ObjectConstIterator &other) const {
    return _slot != other._slot;
  }
  ObjectConstIterator &operator++() {
    _slot = _slot->next();
    return *this;
  }
  ObjectConstIterator &operator+=(size_t distance) {
    _slot = _slot->next(distance);
    return *this;
  }
  const VariantSlot *internal() {
    return _slot;
  }
 private:
  const VariantSlot *_slot;
};
}  // namespace ARDUINOJSON_NAMESPACE
#define JSON_OBJECT_SIZE(NUMBER_OF_ELEMENTS) \
  ((NUMBER_OF_ELEMENTS) * sizeof(ARDUINOJSON_NAMESPACE::VariantSlot))
namespace ARDUINOJSON_NAMESPACE {
template <typename TData>
class ObjectRefBase {
 public:
  operator VariantConstRef() const {
    const void* data = _data;  // prevent warning cast-align
    return VariantConstRef(reinterpret_cast<const VariantData*>(data));
  }
  template <typename TVisitor>
  typename TVisitor::result_type accept(TVisitor& visitor) const {
    return objectAccept(_data, visitor);
  }
  FORCE_INLINE bool isNull() const {
    return _data == 0;
  }
  FORCE_INLINE operator bool() const {
    return _data != 0;
  }
  FORCE_INLINE size_t memoryUsage() const {
    return _data ? _data->memoryUsage() : 0;
  }
  FORCE_INLINE size_t nesting() const {
    return _data ? _data->nesting() : 0;
  }
  FORCE_INLINE size_t size() const {
    return _data ? _data->size() : 0;
  }
 protected:
  ObjectRefBase(TData* data) : _data(data) {}
  TData* _data;
};
class ObjectConstRef : public ObjectRefBase<const CollectionData>,
                       public Visitable {
  friend class ObjectRef;
  typedef ObjectRefBase<const CollectionData> base_type;
 public:
  typedef ObjectConstIterator iterator;
  ObjectConstRef() : base_type(0) {}
  ObjectConstRef(const CollectionData* data) : base_type(data) {}
  FORCE_INLINE iterator begin() const {
    if (!_data)
      return iterator();
    return iterator(_data->head());
  }
  FORCE_INLINE iterator end() const {
    return iterator();
  }
  template <typename TString>
  FORCE_INLINE bool containsKey(const TString& key) const {
    return !getMember(key).isUnbound();
  }
  template <typename TChar>
  FORCE_INLINE bool containsKey(TChar* key) const {
    return !getMember(key).isUnbound();
  }
  template <typename TString>
  FORCE_INLINE VariantConstRef getMember(const TString& key) const {
    return get_impl(adaptString(key));
  }
  template <typename TChar>
  FORCE_INLINE VariantConstRef getMember(TChar* key) const {
    return get_impl(adaptString(key));
  }
  template <typename TString>
  FORCE_INLINE
      typename enable_if<IsString<TString>::value, VariantConstRef>::type
      operator[](const TString& key) const {
    return get_impl(adaptString(key));
  }
  template <typename TChar>
  FORCE_INLINE
      typename enable_if<IsString<TChar*>::value, VariantConstRef>::type
      operator[](TChar* key) const {
    return get_impl(adaptString(key));
  }
  FORCE_INLINE bool operator==(ObjectConstRef rhs) const {
    return objectEquals(_data, rhs._data);
  }
 private:
  template <typename TAdaptedString>
  FORCE_INLINE VariantConstRef get_impl(TAdaptedString key) const {
    return VariantConstRef(objectGetMember(_data, key));
  }
};
class ObjectRef : public ObjectRefBase<CollectionData>,
                  public ObjectShortcuts<ObjectRef>,
                  public Visitable {
  typedef ObjectRefBase<CollectionData> base_type;
 public:
  typedef ObjectIterator iterator;
  FORCE_INLINE ObjectRef() : base_type(0), _pool(0) {}
  FORCE_INLINE ObjectRef(MemoryPool* buf, CollectionData* data)
      : base_type(data), _pool(buf) {}
  operator VariantRef() const {
    void* data = _data;  // prevent warning cast-align
    return VariantRef(_pool, reinterpret_cast<VariantData*>(data));
  }
  operator ObjectConstRef() const {
    return ObjectConstRef(_data);
  }
  FORCE_INLINE iterator begin() const {
    if (!_data)
      return iterator();
    return iterator(_pool, _data->head());
  }
  FORCE_INLINE iterator end() const {
    return iterator();
  }
  void clear() const {
    if (!_data)
      return;
    _data->clear();
  }
  FORCE_INLINE bool set(ObjectConstRef src) {
    if (!_data || !src._data)
      return false;
    return _data->copyFrom(*src._data, _pool);
  }
  template <typename TString>
  FORCE_INLINE VariantRef getMember(const TString& key) const {
    return VariantRef(_pool, objectGetMember(_data, adaptString(key)));
  }
  template <typename TChar>
  FORCE_INLINE VariantRef getMember(TChar* key) const {
    return VariantRef(_pool, objectGetMember(_data, adaptString(key)));
  }
  template <typename TString>
  FORCE_INLINE VariantRef getOrAddMember(const TString& key) const {
    return VariantRef(_pool,
                      objectGetOrAddMember(_data, adaptString(key), _pool,
                                           getStringStoragePolicy(key)));
  }
  template <typename TChar>
  FORCE_INLINE VariantRef getOrAddMember(TChar* key) const {
    return VariantRef(_pool,
                      objectGetOrAddMember(_data, adaptString(key), _pool,
                                           getStringStoragePolicy(key)));
  }
  FORCE_INLINE bool operator==(ObjectRef rhs) const {
    return objectEquals(_data, rhs._data);
  }
  FORCE_INLINE void remove(iterator it) const {
    if (!_data)
      return;
    _data->removeSlot(it.internal());
  }
  template <typename TString>
  FORCE_INLINE void remove(const TString& key) const {
    objectRemove(_data, adaptString(key));
  }
  template <typename TChar>
  FORCE_INLINE void remove(TChar* key) const {
    objectRemove(_data, adaptString(key));
  }
 private:
  MemoryPool* _pool;
};
template <>
struct Converter<ObjectConstRef> {
  static void toJson(VariantConstRef src, VariantRef dst) {
    variantCopyFrom(getData(dst), getData(src), getPool(dst));
  }
  static ObjectConstRef fromJson(VariantConstRef src) {
    return ObjectConstRef(variantAsObject(getData(src)));
  }
  static bool checkJson(VariantConstRef src) {
    const VariantData* data = getData(src);
    return data && data->isObject();
  }
};
template <>
struct Converter<ObjectRef> {
  static void toJson(VariantConstRef src, VariantRef dst) {
    variantCopyFrom(getData(dst), getData(src), getPool(dst));
  }
  static ObjectRef fromJson(VariantRef src) {
    VariantData* data = getData(src);
    MemoryPool* pool = getPool(src);
    return ObjectRef(pool, data != 0 ? data->asObject() : 0);
  }
  static InvalidConversion<VariantConstRef, ObjectRef> fromJson(
      VariantConstRef);
  static bool checkJson(VariantConstRef) {
    return false;
  }
  static bool checkJson(VariantRef src) {
    VariantData* data = getData(src);
    return data && data->isObject();
  }
};
class ArrayRef;
class ObjectRef;
class VariantRef;
template <typename T>
struct VariantTo {};
template <>
struct VariantTo<ArrayRef> {
  typedef ArrayRef type;
};
template <>
struct VariantTo<ObjectRef> {
  typedef ObjectRef type;
};
template <>
struct VariantTo<VariantRef> {
  typedef VariantRef type;
};
}  // namespace ARDUINOJSON_NAMESPACE
#ifdef _MSC_VER
#  pragma warning(push)
#  pragma warning(disable : 4522)
#endif
namespace ARDUINOJSON_NAMESPACE {
template <typename TArray>
class ElementProxy : public VariantOperators<ElementProxy<TArray> >,
                     public VariantShortcuts<ElementProxy<TArray> >,
                     public Visitable,
                     public VariantTag {
  typedef ElementProxy<TArray> this_type;
 public:
  typedef VariantRef variant_type;
  FORCE_INLINE ElementProxy(TArray array, size_t index)
      : _array(array), _index(index) {}
  FORCE_INLINE ElementProxy(const ElementProxy& src)
      : _array(src._array), _index(src._index) {}
  FORCE_INLINE this_type& operator=(const this_type& src) {
    getOrAddUpstreamElement().set(src.as<VariantConstRef>());
    return *this;
  }
  template <typename T>
  FORCE_INLINE this_type& operator=(const T& src) {
    getOrAddUpstreamElement().set(src);
    return *this;
  }
  template <typename T>
  FORCE_INLINE this_type& operator=(T* src) {
    getOrAddUpstreamElement().set(src);
    return *this;
  }
  FORCE_INLINE void clear() const {
    getUpstreamElement().clear();
  }
  FORCE_INLINE bool isNull() const {
    return getUpstreamElement().isNull();
  }
  template <typename T>
  FORCE_INLINE typename enable_if<!is_same<T, char*>::value, T>::type as()
      const {
    return getUpstreamElement().template as<T>();
  }
  template <typename T>
  FORCE_INLINE typename enable_if<is_same<T, char*>::value, const char*>::type
  ARDUINOJSON_DEPRECATED("Replace as<char*>() with as<const char*>()")
      as() const {
    return as<const char*>();
  }
  template <typename T>
  FORCE_INLINE operator T() const {
    return getUpstreamElement();
  }
  template <typename T>
  FORCE_INLINE bool is() const {
    return getUpstreamElement().template is<T>();
  }
  template <typename T>
  FORCE_INLINE typename VariantTo<T>::type to() const {
    return getOrAddUpstreamElement().template to<T>();
  }
  template <typename TValue>
  FORCE_INLINE bool set(const TValue& value) const {
    return getOrAddUpstreamElement().set(value);
  }
  template <typename TValue>
  FORCE_INLINE bool set(TValue* value) const {
    return getOrAddUpstreamElement().set(value);
  }
  template <typename TVisitor>
  typename TVisitor::result_type accept(TVisitor& visitor) const {
    return getUpstreamElement().accept(visitor);
  }
  FORCE_INLINE size_t size() const {
    return getUpstreamElement().size();
  }
  FORCE_INLINE size_t memoryUsage() const {
    return getUpstreamElement().memoryUsage();
  }
  template <typename TNestedKey>
  VariantRef getMember(TNestedKey* key) const {
    return getUpstreamElement().getMember(key);
  }
  template <typename TNestedKey>
  VariantRef getMember(const TNestedKey& key) const {
    return getUpstreamElement().getMember(key);
  }
  template <typename TNestedKey>
  VariantRef getOrAddMember(TNestedKey* key) const {
    return getOrAddUpstreamElement().getOrAddMember(key);
  }
  template <typename TNestedKey>
  VariantRef getOrAddMember(const TNestedKey& key) const {
    return getOrAddUpstreamElement().getOrAddMember(key);
  }
  VariantRef addElement() const {
    return getOrAddUpstreamElement().addElement();
  }
  VariantRef getElement(size_t index) const {
    return getOrAddUpstreamElement().getElement(index);
  }
  VariantRef getOrAddElement(size_t index) const {
    return getOrAddUpstreamElement().getOrAddElement(index);
  }
  FORCE_INLINE void remove(size_t index) const {
    getUpstreamElement().remove(index);
  }
  template <typename TChar>
  FORCE_INLINE typename enable_if<IsString<TChar*>::value>::type remove(
      TChar* key) const {
    getUpstreamElement().remove(key);
  }
  template <typename TString>
  FORCE_INLINE typename enable_if<IsString<TString>::value>::type remove(
      const TString& key) const {
    getUpstreamElement().remove(key);
  }
 private:
  FORCE_INLINE VariantRef getUpstreamElement() const {
    return _array.getElement(_index);
  }
  FORCE_INLINE VariantRef getOrAddUpstreamElement() const {
    return _array.getOrAddElement(_index);
  }
  friend void convertToJson(const this_type& src, VariantRef dst) {
    dst.set(src.getUpstreamElement());
  }
  TArray _array;
  const size_t _index;
};
}  // namespace ARDUINOJSON_NAMESPACE
#ifdef _MSC_VER
#  pragma warning(pop)
#endif
#ifdef _MSC_VER
#  pragma warning(push)
#  pragma warning(disable : 4522)
#endif
namespace ARDUINOJSON_NAMESPACE {
template <typename TObject, typename TStringRef>
class MemberProxy : public VariantOperators<MemberProxy<TObject, TStringRef> >,
                    public VariantShortcuts<MemberProxy<TObject, TStringRef> >,
                    public Visitable,
                    public VariantTag {
  typedef MemberProxy<TObject, TStringRef> this_type;
 public:
  typedef VariantRef variant_type;
  FORCE_INLINE MemberProxy(TObject variant, TStringRef key)
      : _object(variant), _key(key) {}
  FORCE_INLINE MemberProxy(const MemberProxy &src)
      : _object(src._object), _key(src._key) {}
  FORCE_INLINE operator VariantConstRef() const {
    return getUpstreamMember();
  }
  FORCE_INLINE this_type &operator=(const this_type &src) {
    getOrAddUpstreamMember().set(src);
    return *this;
  }
  template <typename TValue>
  FORCE_INLINE typename enable_if<!is_array<TValue>::value, this_type &>::type
  operator=(const TValue &src) {
    getOrAddUpstreamMember().set(src);
    return *this;
  }
  template <typename TChar>
  FORCE_INLINE this_type &operator=(TChar *src) {
    getOrAddUpstreamMember().set(src);
    return *this;
  }
  FORCE_INLINE void clear() const {
    getUpstreamMember().clear();
  }
  FORCE_INLINE bool isNull() const {
    return getUpstreamMember().isNull();
  }
  template <typename T>
  FORCE_INLINE typename enable_if<!is_same<T, char *>::value, T>::type as()
      const {
    return getUpstreamMember().template as<T>();
  }
  template <typename T>
  FORCE_INLINE typename enable_if<is_same<T, char *>::value, const char *>::type
  ARDUINOJSON_DEPRECATED("Replace as<char*>() with as<const char*>()")
      as() const {
    return as<const char *>();
  }
  template <typename T>
  FORCE_INLINE operator T() const {
    return getUpstreamMember();
  }
  template <typename TValue>
  FORCE_INLINE bool is() const {
    return getUpstreamMember().template is<TValue>();
  }
  FORCE_INLINE size_t size() const {
    return getUpstreamMember().size();
  }
  FORCE_INLINE size_t memoryUsage() const {
    return getUpstreamMember().memoryUsage();
  }
  FORCE_INLINE void remove(size_t index) const {
    getUpstreamMember().remove(index);
  }
  template <typename TChar>
  FORCE_INLINE typename enable_if<IsString<TChar *>::value>::type remove(
      TChar *key) const {
    getUpstreamMember().remove(key);
  }
  template <typename TString>
  FORCE_INLINE typename enable_if<IsString<TString>::value>::type remove(
      const TString &key) const {
    getUpstreamMember().remove(key);
  }
  template <typename TValue>
  FORCE_INLINE typename VariantTo<TValue>::type to() {
    return getOrAddUpstreamMember().template to<TValue>();
  }
  template <typename TValue>
  FORCE_INLINE bool set(const TValue &value) {
    return getOrAddUpstreamMember().set(value);
  }
  template <typename TChar>
  FORCE_INLINE bool set(TChar *value) {
    return getOrAddUpstreamMember().set(value);
  }
  template <typename TVisitor>
  typename TVisitor::result_type accept(TVisitor &visitor) const {
    return getUpstreamMember().accept(visitor);
  }
  FORCE_INLINE VariantRef addElement() const {
    return getOrAddUpstreamMember().addElement();
  }
  FORCE_INLINE VariantRef getElement(size_t index) const {
    return getUpstreamMember().getElement(index);
  }
  FORCE_INLINE VariantRef getOrAddElement(size_t index) const {
    return getOrAddUpstreamMember().getOrAddElement(index);
  }
  template <typename TChar>
  FORCE_INLINE VariantRef getMember(TChar *key) const {
    return getUpstreamMember().getMember(key);
  }
  template <typename TString>
  FORCE_INLINE VariantRef getMember(const TString &key) const {
    return getUpstreamMember().getMember(key);
  }
  template <typename TChar>
  FORCE_INLINE VariantRef getOrAddMember(TChar *key) const {
    return getOrAddUpstreamMember().getOrAddMember(key);
  }
  template <typename TString>
  FORCE_INLINE VariantRef getOrAddMember(const TString &key) const {
    return getOrAddUpstreamMember().getOrAddMember(key);
  }
 private:
  FORCE_INLINE VariantRef getUpstreamMember() const {
    return _object.getMember(_key);
  }
  FORCE_INLINE VariantRef getOrAddUpstreamMember() const {
    return _object.getOrAddMember(_key);
  }
  friend void convertToJson(const this_type &src, VariantRef dst) {
    dst.set(src.getUpstreamMember());
  }
  TObject _object;
  TStringRef _key;
};
}  // namespace ARDUINOJSON_NAMESPACE
#ifdef _MSC_VER
#  pragma warning(pop)
#endif
namespace ARDUINOJSON_NAMESPACE {
class JsonDocument : public Visitable,
                     public VariantOperators<const JsonDocument&> {
 public:
  template <typename TVisitor>
  typename TVisitor::result_type accept(TVisitor& visitor) const {
    return getVariant().accept(visitor);
  }
  template <typename T>
  T as() {
    return getVariant().template as<T>();
  }
  template <typename T>
  T as() const {
    return getVariant().template as<T>();
  }
  void clear() {
    _pool.clear();
    _data.init();
  }
  template <typename T>
  bool is() {
    return getVariant().template is<T>();
  }
  template <typename T>
  bool is() const {
    return getVariant().template is<T>();
  }
  bool isNull() const {
    return getVariant().isNull();
  }
  size_t memoryUsage() const {
    return _pool.size();
  }
  bool overflowed() const {
    return _pool.overflowed();
  }
  size_t nesting() const {
    return _data.nesting();
  }
  size_t capacity() const {
    return _pool.capacity();
  }
  size_t size() const {
    return _data.size();
  }
  bool set(const JsonDocument& src) {
    return to<VariantRef>().set(src.as<VariantConstRef>());
  }
  template <typename T>
  typename enable_if<!is_base_of<JsonDocument, T>::value, bool>::type set(
      const T& src) {
    return to<VariantRef>().set(src);
  }
  template <typename T>
  typename VariantTo<T>::type to() {
    clear();
    return getVariant().template to<T>();
  }
  MemoryPool& memoryPool() {
    return _pool;
  }
  VariantData& data() {
    return _data;
  }
  ArrayRef createNestedArray() {
    return addElement().to<ArrayRef>();
  }
  template <typename TChar>
  ArrayRef createNestedArray(TChar* key) {
    return getOrAddMember(key).template to<ArrayRef>();
  }
  template <typename TString>
  ArrayRef createNestedArray(const TString& key) {
    return getOrAddMember(key).template to<ArrayRef>();
  }
  ObjectRef createNestedObject() {
    return addElement().to<ObjectRef>();
  }
  template <typename TChar>
  ObjectRef createNestedObject(TChar* key) {
    return getOrAddMember(key).template to<ObjectRef>();
  }
  template <typename TString>
  ObjectRef createNestedObject(const TString& key) {
    return getOrAddMember(key).template to<ObjectRef>();
  }
  template <typename TChar>
  bool containsKey(TChar* key) const {
    return !getMember(key).isUnbound();
  }
  template <typename TString>
  bool containsKey(const TString& key) const {
    return !getMember(key).isUnbound();
  }
  template <typename TString>
  FORCE_INLINE typename enable_if<IsString<TString>::value,
                                  MemberProxy<JsonDocument&, TString> >::type
  operator[](const TString& key) {
    return MemberProxy<JsonDocument&, TString>(*this, key);
  }
  template <typename TChar>
  FORCE_INLINE typename enable_if<IsString<TChar*>::value,
                                  MemberProxy<JsonDocument&, TChar*> >::type
  operator[](TChar* key) {
    return MemberProxy<JsonDocument&, TChar*>(*this, key);
  }
  template <typename TString>
  FORCE_INLINE
      typename enable_if<IsString<TString>::value, VariantConstRef>::type
      operator[](const TString& key) const {
    return getMember(key);
  }
  template <typename TChar>
  FORCE_INLINE
      typename enable_if<IsString<TChar*>::value, VariantConstRef>::type
      operator[](TChar* key) const {
    return getMember(key);
  }
  FORCE_INLINE ElementProxy<JsonDocument&> operator[](size_t index) {
    return ElementProxy<JsonDocument&>(*this, index);
  }
  FORCE_INLINE VariantConstRef operator[](size_t index) const {
    return getElement(index);
  }
  FORCE_INLINE VariantRef getElement(size_t index) {
    return VariantRef(&_pool, _data.getElement(index));
  }
  FORCE_INLINE VariantConstRef getElement(size_t index) const {
    return VariantConstRef(_data.getElement(index));
  }
  FORCE_INLINE VariantRef getOrAddElement(size_t index) {
    return VariantRef(&_pool, _data.getOrAddElement(index, &_pool));
  }
  template <typename TChar>
  FORCE_INLINE VariantConstRef getMember(TChar* key) const {
    return VariantConstRef(_data.getMember(adaptString(key)));
  }
  template <typename TString>
  FORCE_INLINE
      typename enable_if<IsString<TString>::value, VariantConstRef>::type
      getMember(const TString& key) const {
    return VariantConstRef(_data.getMember(adaptString(key)));
  }
  template <typename TChar>
  FORCE_INLINE VariantRef getMember(TChar* key) {
    return VariantRef(&_pool, _data.getMember(adaptString(key)));
  }
  template <typename TString>
  FORCE_INLINE typename enable_if<IsString<TString>::value, VariantRef>::type
  getMember(const TString& key) {
    return VariantRef(&_pool, _data.getMember(adaptString(key)));
  }
  template <typename TChar>
  FORCE_INLINE VariantRef getOrAddMember(TChar* key) {
    return VariantRef(&_pool,
                      _data.getOrAddMember(adaptString(key), &_pool,
                                           getStringStoragePolicy(key)));
  }
  template <typename TString>
  FORCE_INLINE VariantRef getOrAddMember(const TString& key) {
    return VariantRef(&_pool,
                      _data.getOrAddMember(adaptString(key), &_pool,
                                           getStringStoragePolicy(key)));
  }
  FORCE_INLINE VariantRef addElement() {
    return VariantRef(&_pool, _data.addElement(&_pool));
  }
  template <typename TValue>
  FORCE_INLINE bool add(const TValue& value) {
    return addElement().set(value);
  }
  template <typename TChar>
  FORCE_INLINE bool add(TChar* value) {
    return addElement().set(value);
  }
  FORCE_INLINE void remove(size_t index) {
    _data.remove(index);
  }
  template <typename TChar>
  FORCE_INLINE typename enable_if<IsString<TChar*>::value>::type remove(
      TChar* key) {
    _data.remove(adaptString(key));
  }
  template <typename TString>
  FORCE_INLINE typename enable_if<IsString<TString>::value>::type remove(
      const TString& key) {
    _data.remove(adaptString(key));
  }
  FORCE_INLINE operator VariantRef() {
    return getVariant();
  }
  FORCE_INLINE operator VariantConstRef() const {
    return getVariant();
  }
 protected:
  JsonDocument() : _pool(0, 0) {
    _data.init();
  }
  JsonDocument(MemoryPool pool) : _pool(pool) {
    _data.init();
  }
  JsonDocument(char* buf, size_t capa) : _pool(buf, capa) {
    _data.init();
  }
  ~JsonDocument() {}
  void replacePool(MemoryPool pool) {
    _pool = pool;
  }
  VariantRef getVariant() {
    return VariantRef(&_pool, &_data);
  }
  VariantConstRef getVariant() const {
    return VariantConstRef(&_data);
  }
  MemoryPool _pool;
  VariantData _data;
 private:
  JsonDocument(const JsonDocument&);
  JsonDocument& operator=(const JsonDocument&);
};
inline void convertToJson(const JsonDocument& src, VariantRef dst) {
  dst.set(src.as<VariantConstRef>());
}
template <typename TAllocator>
class AllocatorOwner {
 public:
  AllocatorOwner() {}
  AllocatorOwner(TAllocator a) : _allocator(a) {}
  void* allocate(size_t size) {
    return _allocator.allocate(size);
  }
  void deallocate(void* ptr) {
    if (ptr)
      _allocator.deallocate(ptr);
  }
  void* reallocate(void* ptr, size_t new_size) {
    return _allocator.reallocate(ptr, new_size);
  }
  TAllocator& allocator() {
    return _allocator;
  }
 private:
  TAllocator _allocator;
};
template <typename TAllocator>
class BasicJsonDocument : AllocatorOwner<TAllocator>, public JsonDocument {
 public:
  explicit BasicJsonDocument(size_t capa, TAllocator alloc = TAllocator())
      : AllocatorOwner<TAllocator>(alloc), JsonDocument(allocPool(capa)) {}
  BasicJsonDocument(const BasicJsonDocument& src)
      : AllocatorOwner<TAllocator>(src), JsonDocument() {
    copyAssignFrom(src);
  }
#if ARDUINOJSON_HAS_RVALUE_REFERENCES
  BasicJsonDocument(BasicJsonDocument&& src) : AllocatorOwner<TAllocator>(src) {
    moveAssignFrom(src);
  }
#endif
  BasicJsonDocument(const JsonDocument& src) {
    copyAssignFrom(src);
  }
  template <typename T>
  BasicJsonDocument(
      const T& src,
      typename enable_if<
          is_same<T, VariantRef>::value || is_same<T, VariantConstRef>::value ||
          is_same<T, ArrayRef>::value || is_same<T, ArrayConstRef>::value ||
          is_same<T, ObjectRef>::value ||
          is_same<T, ObjectConstRef>::value>::type* = 0)
      : JsonDocument(allocPool(src.memoryUsage())) {
    set(src);
  }
  BasicJsonDocument(VariantRef src)
      : JsonDocument(allocPool(src.memoryUsage())) {
    set(src);
  }
  ~BasicJsonDocument() {
    freePool();
  }
  BasicJsonDocument& operator=(const BasicJsonDocument& src) {
    copyAssignFrom(src);
    return *this;
  }
#if ARDUINOJSON_HAS_RVALUE_REFERENCES
  BasicJsonDocument& operator=(BasicJsonDocument&& src) {
    moveAssignFrom(src);
    return *this;
  }
#endif
  template <typename T>
  BasicJsonDocument& operator=(const T& src) {
    size_t requiredSize = src.memoryUsage();
    if (requiredSize > capacity())
      reallocPool(requiredSize);
    set(src);
    return *this;
  }
  void shrinkToFit() {
    ptrdiff_t bytes_reclaimed = _pool.squash();
    if (bytes_reclaimed == 0)
      return;
    void* old_ptr = _pool.buffer();
    void* new_ptr = this->reallocate(old_ptr, _pool.capacity());
    ptrdiff_t ptr_offset =
        static_cast<char*>(new_ptr) - static_cast<char*>(old_ptr);
    _pool.movePointers(ptr_offset);
    _data.movePointers(ptr_offset, ptr_offset - bytes_reclaimed);
  }
  bool garbageCollect() {
    BasicJsonDocument tmp(*this);
    if (!tmp.capacity())
      return false;
    tmp.set(*this);
    moveAssignFrom(tmp);
    return true;
  }
  using AllocatorOwner<TAllocator>::allocator;
 private:
  MemoryPool allocPool(size_t requiredSize) {
    size_t capa = addPadding(requiredSize);
    return MemoryPool(reinterpret_cast<char*>(this->allocate(capa)), capa);
  }
  void reallocPool(size_t requiredSize) {
    size_t capa = addPadding(requiredSize);
    if (capa == _pool.capacity())
      return;
    freePool();
    replacePool(allocPool(addPadding(requiredSize)));
  }
  void freePool() {
    this->deallocate(memoryPool().buffer());
  }
  void copyAssignFrom(const JsonDocument& src) {
    reallocPool(src.capacity());
    set(src);
  }
  void moveAssignFrom(BasicJsonDocument& src) {
    freePool();
    _data = src._data;
    _pool = src._pool;
    src._data.setNull();
    src._pool = MemoryPool(0, 0);
  }
};
}  // namespace ARDUINOJSON_NAMESPACE
#include <stdlib.h>
namespace ARDUINOJSON_NAMESPACE {
struct DefaultAllocator {
  void* allocate(size_t size) {
    return malloc(size);
  }
  void deallocate(void* ptr) {
    free(ptr);
  }
  void* reallocate(void* ptr, size_t new_size) {
    return realloc(ptr, new_size);
  }
};
typedef BasicJsonDocument<DefaultAllocator> DynamicJsonDocument;
template <size_t desiredCapacity>
class StaticJsonDocument : public JsonDocument {
  static const size_t _capacity =
      AddPadding<Max<1, desiredCapacity>::value>::value;
 public:
  StaticJsonDocument() : JsonDocument(_buffer, _capacity) {}
  StaticJsonDocument(const StaticJsonDocument& src)
      : JsonDocument(_buffer, _capacity) {
    set(src);
  }
  template <typename T>
  StaticJsonDocument(const T& src,
                     typename enable_if<IsVisitable<T>::value>::type* = 0)
      : JsonDocument(_buffer, _capacity) {
    set(src);
  }
  StaticJsonDocument(VariantRef src) : JsonDocument(_buffer, _capacity) {
    set(src);
  }
  StaticJsonDocument& operator=(const StaticJsonDocument& src) {
    set(src);
    return *this;
  }
  template <typename T>
  StaticJsonDocument& operator=(const T& src) {
    set(src);
    return *this;
  }
  void garbageCollect() {
    StaticJsonDocument tmp(*this);
    set(tmp);
  }
 private:
  char _buffer[_capacity];
};
template <typename TArray>
inline ArrayRef ArrayShortcuts<TArray>::createNestedArray() const {
  return impl()->addElement().template to<ArrayRef>();
}
template <typename TArray>
inline ObjectRef ArrayShortcuts<TArray>::createNestedObject() const {
  return impl()->addElement().template to<ObjectRef>();
}
template <typename TArray>
inline ElementProxy<TArray> ArrayShortcuts<TArray>::operator[](
    size_t index) const {
  return ElementProxy<TArray>(*impl(), index);
}
template <typename T>
inline typename enable_if<!is_array<T>::value, bool>::type copyArray(
    const T& src, VariantRef dst) {
  return dst.set(src);
}
template <typename T, size_t N, typename TDestination>
inline typename enable_if<!is_base_of<JsonDocument, TDestination>::value,
                          bool>::type
copyArray(T (&src)[N], const TDestination& dst) {
  return copyArray(src, N, dst);
}
template <typename T, typename TDestination>
inline typename enable_if<!is_base_of<JsonDocument, TDestination>::value,
                          bool>::type
copyArray(const T* src, size_t len, const TDestination& dst) {
  bool ok = true;
  for (size_t i = 0; i < len; i++) {
    ok &= copyArray(src[i], dst.addElement());
  }
  return ok;
}
template <typename TDestination>
inline bool copyArray(const char* src, size_t, const TDestination& dst) {
  return dst.set(src);
}
template <typename T>
inline bool copyArray(const T& src, JsonDocument& dst) {
  return copyArray(src, dst.to<ArrayRef>());
}
template <typename T>
inline bool copyArray(const T* src, size_t len, JsonDocument& dst) {
  return copyArray(src, len, dst.to<ArrayRef>());
}
template <typename T>
inline typename enable_if<!is_array<T>::value, size_t>::type copyArray(
    VariantConstRef src, T& dst) {
  dst = src.as<T>();
  return 1;
}
template <typename T, size_t N>
inline size_t copyArray(ArrayConstRef src, T (&dst)[N]) {
  return copyArray(src, dst, N);
}
template <typename T>
inline size_t copyArray(ArrayConstRef src, T* dst, size_t len) {
  size_t i = 0;
  for (ArrayConstRef::iterator it = src.begin(); it != src.end() && i < len;
       ++it)
    copyArray(*it, dst[i++]);
  return i;
}
template <size_t N>
inline size_t copyArray(VariantConstRef src, char (&dst)[N]) {
  String s = src;
  size_t len = N - 1;
  if (len > s.size())
    len = s.size();
  memcpy(dst, s.c_str(), len);
  dst[len] = 0;
  return 1;
}
template <typename TSource, typename T>
inline typename enable_if<is_array<T>::value &&
                              is_base_of<JsonDocument, TSource>::value,
                          size_t>::type
copyArray(const TSource& src, T& dst) {
  return copyArray(src.template as<ArrayConstRef>(), dst);
}
inline bool variantEquals(const VariantData* a, const VariantData* b) {
  return variantCompare(a, b) == COMPARE_RESULT_EQUAL;
}
inline VariantSlot* CollectionData::addSlot(MemoryPool* pool) {
  VariantSlot* slot = pool->allocVariant();
  if (!slot)
    return 0;
  if (_tail) {
    _tail->setNextNotNull(slot);
    _tail = slot;
  } else {
    _head = slot;
    _tail = slot;
  }
  slot->clear();
  return slot;
}
inline VariantData* CollectionData::addElement(MemoryPool* pool) {
  return slotData(addSlot(pool));
}
template <typename TAdaptedString, typename TStoragePolicy>
inline VariantData* CollectionData::addMember(TAdaptedString key,
                                              MemoryPool* pool,
                                              TStoragePolicy storage) {
  VariantSlot* slot = addSlot(pool);
  if (!slotSetKey(slot, key, pool, storage)) {
    removeSlot(slot);
    return 0;
  }
  return slot->data();
}
inline void CollectionData::clear() {
  _head = 0;
  _tail = 0;
}
template <typename TAdaptedString>
inline bool CollectionData::containsKey(const TAdaptedString& key) const {
  return getSlot(key) != 0;
}
inline bool CollectionData::copyFrom(const CollectionData& src,
                                     MemoryPool* pool) {
  clear();
  for (VariantSlot* s = src._head; s; s = s->next()) {
    VariantData* var;
    if (s->key() != 0) {
      String key(s->key(), s->ownsKey() ? String::Copied : String::Linked);
      var = addMember(adaptString(key), pool, getStringStoragePolicy(key));
    } else {
      var = addElement(pool);
    }
    if (!var)
      return false;
    if (!var->copyFrom(*s->data(), pool))
      return false;
  }
  return true;
}
inline bool CollectionData::equalsObject(const CollectionData& other) const {
  size_t count = 0;
  for (VariantSlot* slot = _head; slot; slot = slot->next()) {
    VariantData* v1 = slot->data();
    VariantData* v2 = other.getMember(adaptString(slot->key()));
    if (!variantEquals(v1, v2))
      return false;
    count++;
  }
  return count == other.size();
}
inline bool CollectionData::equalsArray(const CollectionData& other) const {
  VariantSlot* s1 = _head;
  VariantSlot* s2 = other._head;
  for (;;) {
    if (s1 == s2)
      return true;
    if (!s1 || !s2)
      return false;
    if (!variantEquals(s1->data(), s2->data()))
      return false;
    s1 = s1->next();
    s2 = s2->next();
  }
}
template <typename TAdaptedString>
inline VariantSlot* CollectionData::getSlot(TAdaptedString key) const {
  if (key.isNull())
    return 0;
  VariantSlot* slot = _head;
  while (slot) {
    if (stringEquals(key, adaptString(slot->key())))
      break;
    slot = slot->next();
  }
  return slot;
}
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
